3lkgrove/VoronZero/STLs/V0/Toolheads/Hotend_Mounts/Standard/[a]_Hotend_Mount_Revo_Voron.stl

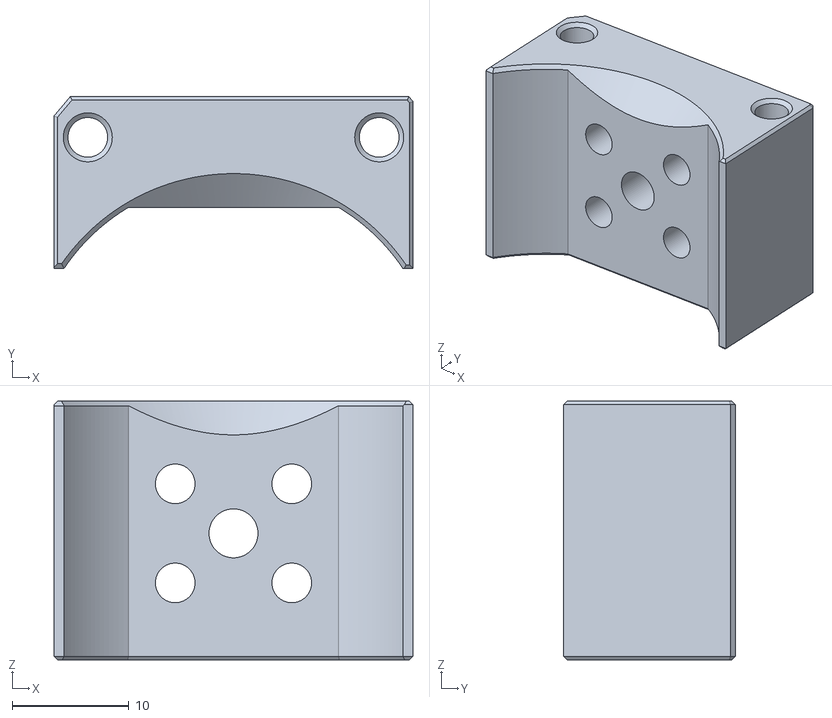
[picture p17: CAD file, 2025-04-02]
STLs/V0/Toolheads/Hotend_Mounts/Standard/[a]_Hotend_Mount_Revo_Voron.stl
30.8 x 14.7 x 22.2
