3lkgrove/VoronZero/STLs/V0/Toolheads/Mini_Stealthburner/[a]_MiniSB_Motor_Plate_x1.stl

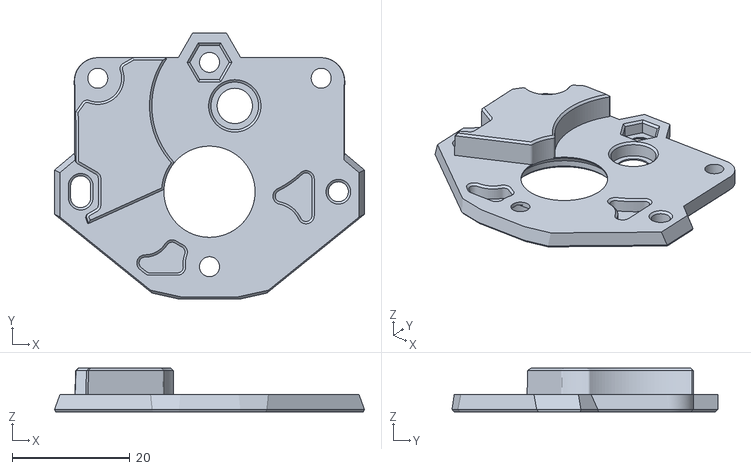
[picture p18: CAD file, 2025-04-02]
STLs/V0/Toolheads/Mini_Stealthburner/[a]_MiniSB_Motor_Plate_x1.stl
52.7 x 45.2 x 7.40
