3lkgrove/VoronZero/STLs/V0/Tools/V0_Extrusion_Drilling_Guide_x1.STL

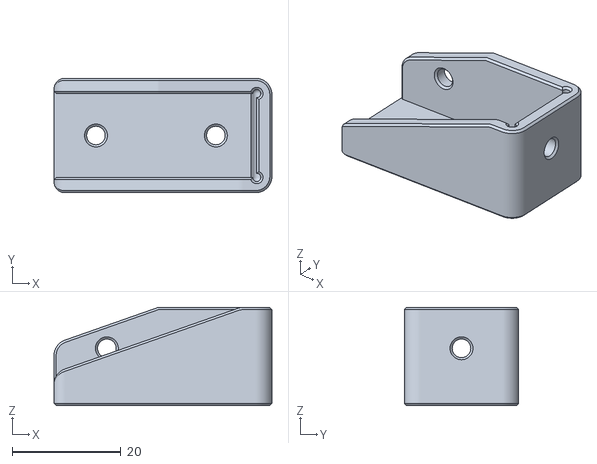
[picture p19: CAD file, 2025-04-02]
STLs/V0/Tools/V0_Extrusion_Drilling_Guide_x1.STL
40.0 x 21.0 x 18.0
