3lkgrove/VoronZero/STLs/V0/Tophat/TH_Lower_Clip_Mirror_x3.stl

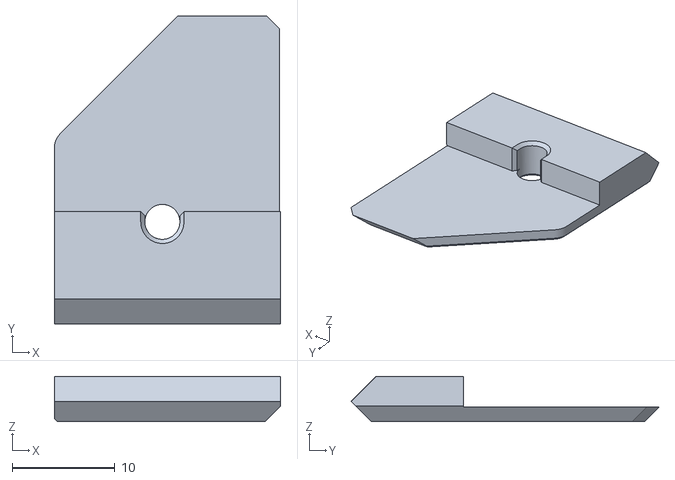
[picture p20: CAD file, 2025-04-02]
STLs/V0/Tophat/TH_Lower_Clip_Mirror_x3.stl
22.0 x 29.9 x 4.40
