3lkgrove/VoronZero/STLs/V0/XY_Joint_Left_Lower_x1.stl

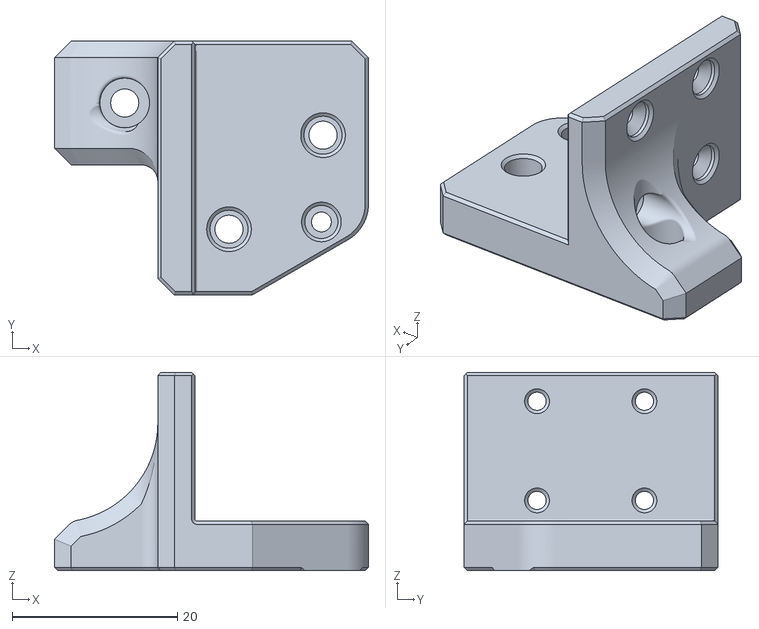
[picture p21: CAD file, 2025-04-02]
STLs/V0/XY_Joint_Left_Lower_x1.stl
38.0 x 30.7 x 24.0
