3lkgrove/VoronZero/STLs/Kirigami/VORON_v0.2_stealth_chain_mount_5mm_spacer.stl

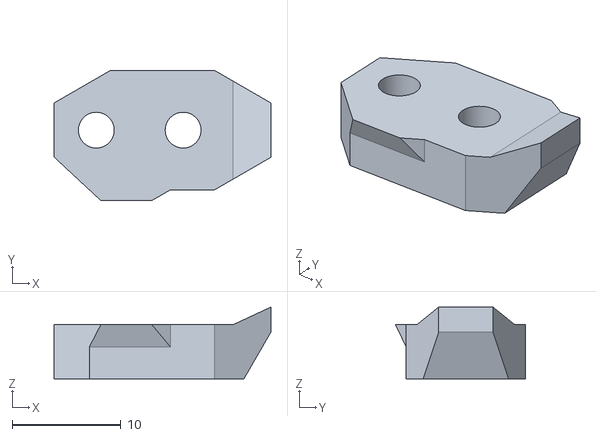
[picture p22: CAD file, 2025-04-02]
STLs/Kirigami/VORON_v0.2_stealth_chain_mount_5mm_spacer.stl
20.0 x 12.0 x 6.63
