3lkgrove/VoronZero/STLs/Umbilical/ToolheadSpacer_with_StrainRelief.STL

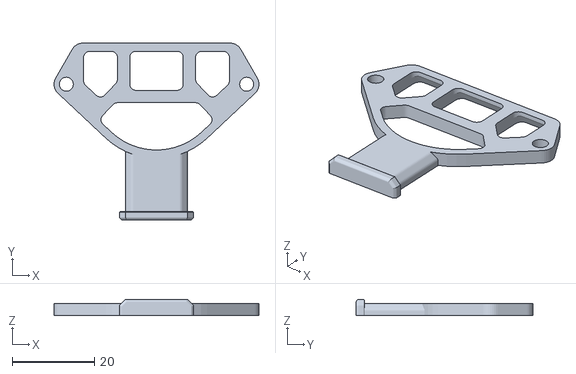
[picture p23: CAD file, 2025-04-06]
STLs/Umbilical/ToolheadSpacer_with_StrainRelief.STL
49.8 x 43.0 x 4.00
