3lkgrove/VoronZero/STLs/V0/Display/[a]_Display_Faceplate_x1.stl

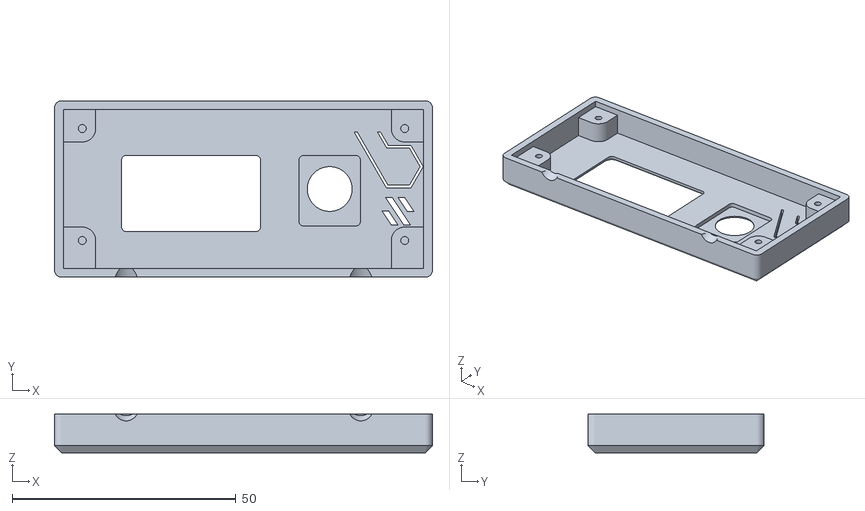
[picture p24: CAD file, 2025-04-02]
STLs/V0/Display/[a]_Display_Faceplate_x1.stl
84.4 x 39.4 x 8.63
