3lkgrove/VoronZero/STLs/V0/Electronics/RPi_or_BTT-Pico_Mount.STL

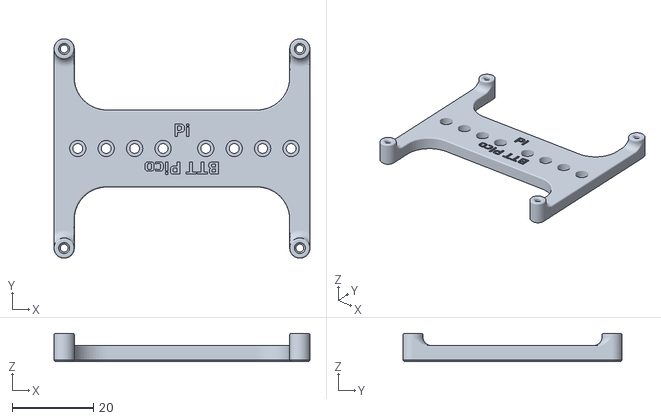
[picture p25: CAD file, 2025-04-02]
STLs/V0/Electronics/RPi_or_BTT-Pico_Mount.STL
63.0 x 54.0 x 7.00
