3lkgrove/VoronZero/STLs/V0/Multibody_STLs/Skirts/Front_Left_Skirt_Multibody_x1.stl

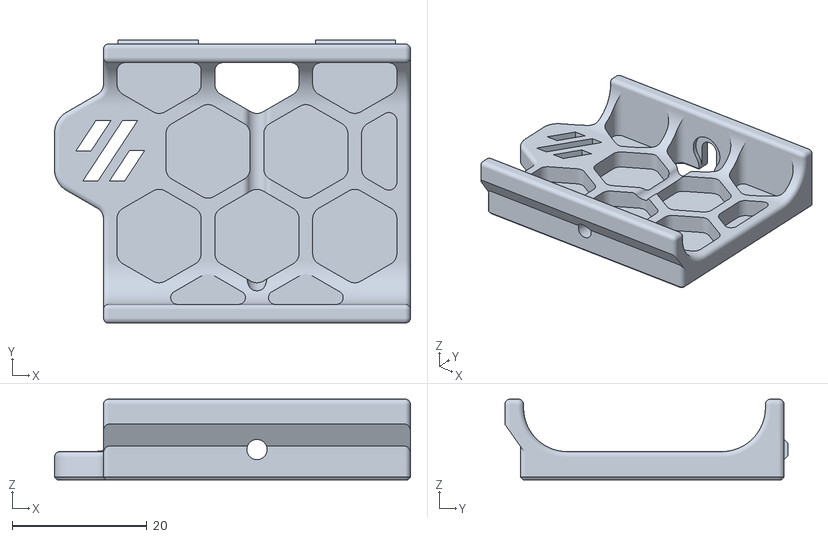
[picture p26: CAD file, 2025-04-02]
STLs/V0/Multibody_STLs/Skirts/Front_Left_Skirt_Multibody_x1.stl
52.9 x 42.1 x 12.0
