3lkgrove/VoronZero/STLs/V0/Skirts/Foot_Rear_Right_Plain.STL

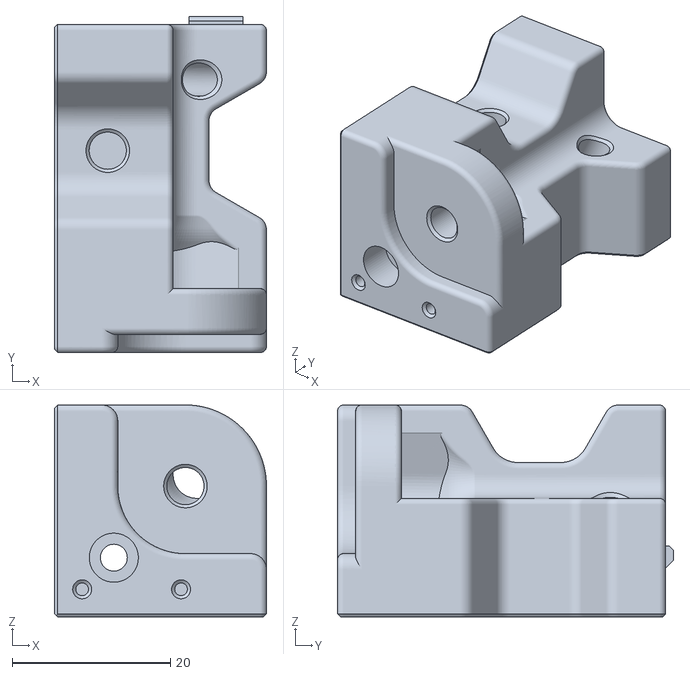
[picture p27: CAD file, 2025-04-02]
STLs/V0/Skirts/Foot_Rear_Right_Plain.STL
26.8 x 42.5 x 26.8
