3lkgrove/VoronZero/STLs/V0/Toolheads/ADXL_Mounts/MiniSB_adxl_mount_adafruit_19mm.stl

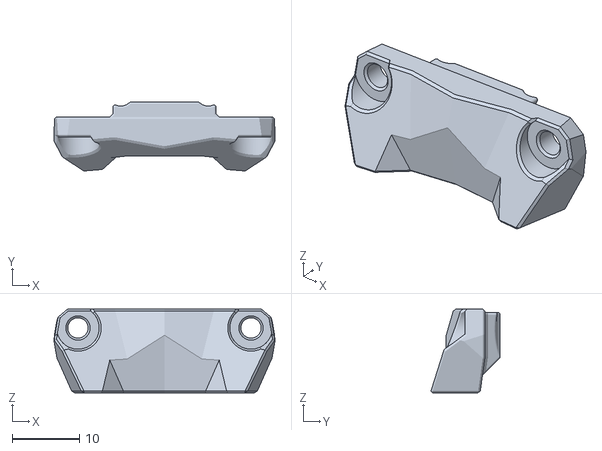
[picture p28: CAD file, 2025-04-02]
STLs/V0/Toolheads/ADXL_Mounts/MiniSB_adxl_mount_adafruit_19mm.stl
32.8 x 10.2 x 12.4
