3lkgrove/VoronZero/STLs/V0/Toolheads/Hotend_Mounts/Standard/[a]_Hotend_Mount_Formbot.stl

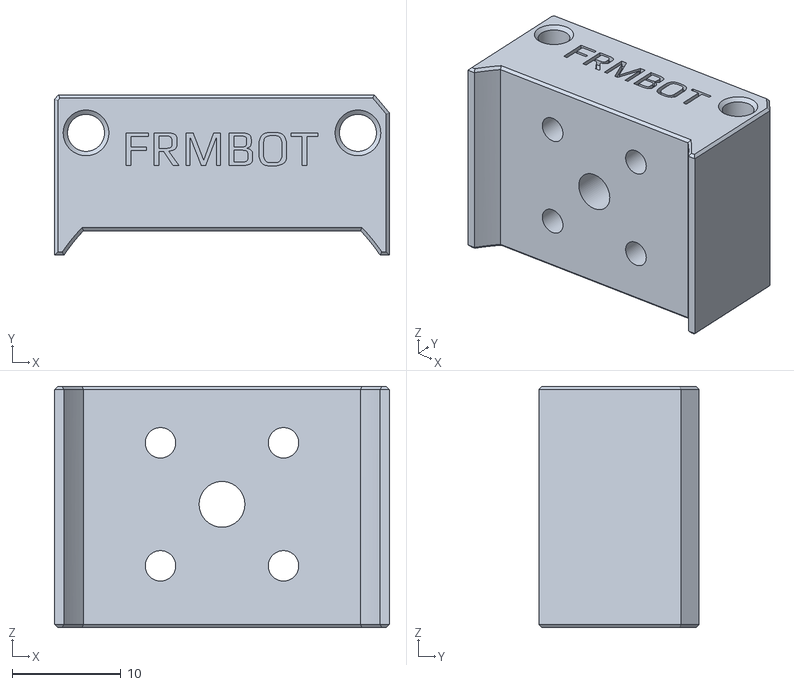
[picture p30: CAD file, 2025-04-02]
STLs/V0/Toolheads/Hotend_Mounts/Standard/[a]_Hotend_Mount_Formbot.stl
30.8 x 14.7 x 22.2
