3lkgrove/VoronZero/STLs/V0/Toolheads/Mini_Stealthburner/[a]_Guidler_x1.STL

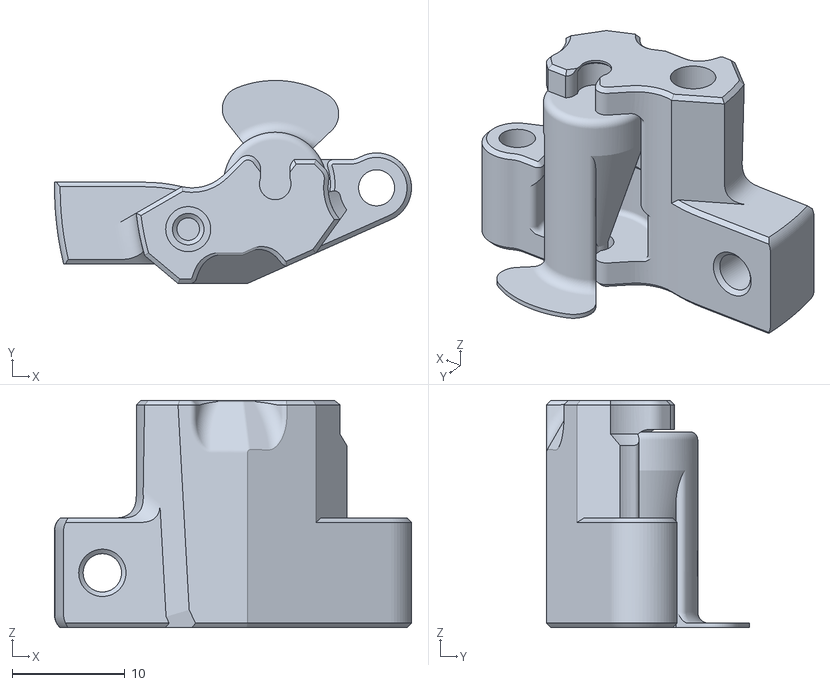
[picture p31: CAD file, 2025-04-02]
STLs/V0/Toolheads/Mini_Stealthburner/[a]_Guidler_x1.STL
31.7 x 18.0 x 20.2
