3lkgrove/VoronZero/STLs/V0/Tophat/TH_Hinge_A_Top_x1.stl

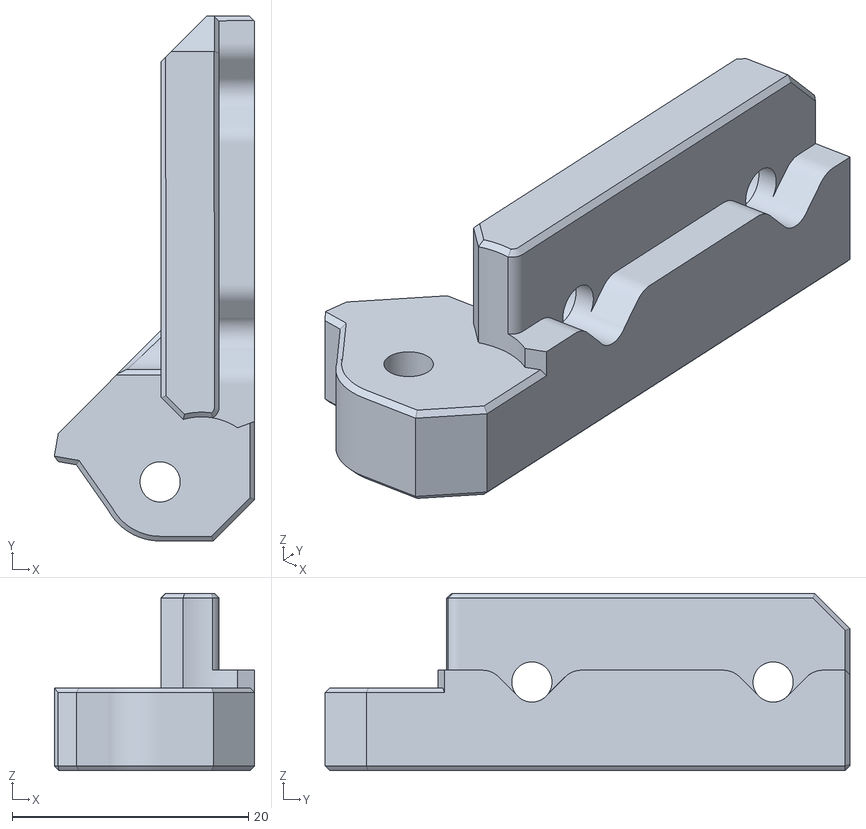
[picture p32: CAD file, 2025-04-02]
STLs/V0/Tophat/TH_Hinge_A_Top_x1.stl
17.0 x 44.4 x 15.0
