3lkgrove/VoronZero/STLs/Umbilical/FramePCBCover.STL

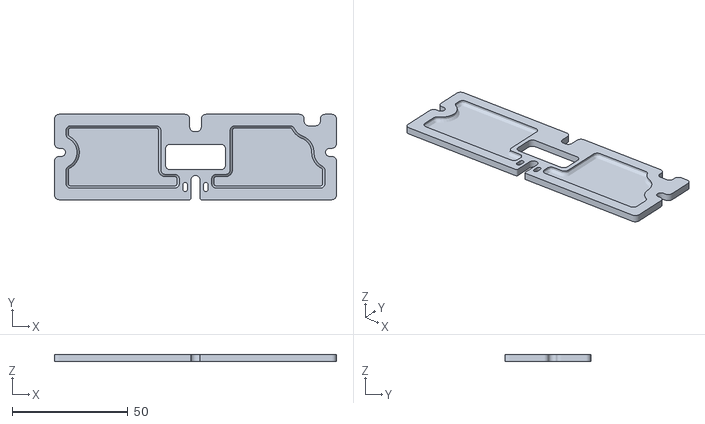
[picture p33: CAD file, 2025-04-06]
STLs/Umbilical/FramePCBCover.STL
122.0 x 37.0 x 3.00
