3lkgrove/VoronZero/STLs/V0/Display/Display_Knob_x1.stl

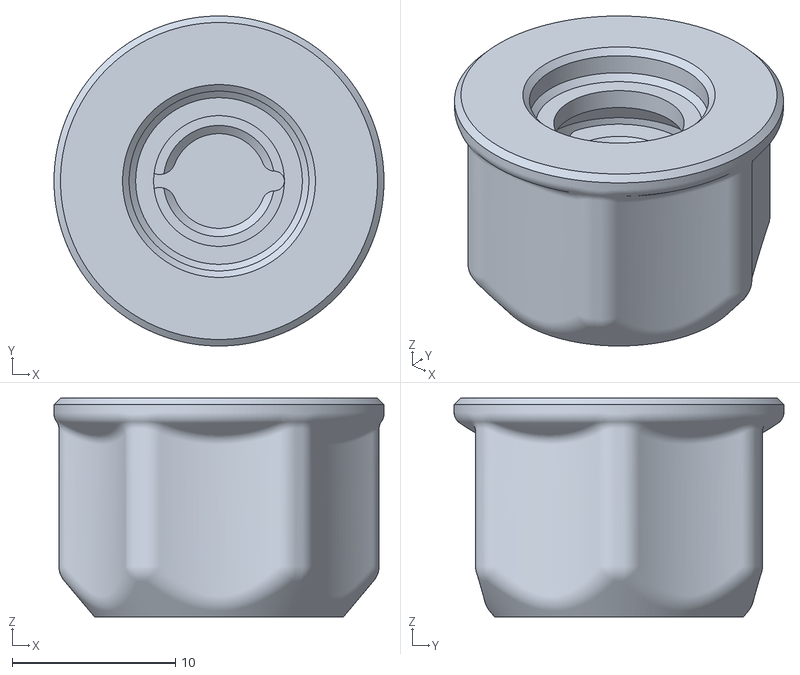
[picture p34: CAD file, 2025-04-02]
STLs/V0/Display/Display_Knob_x1.stl
20.2 x 20.2 x 13.4
