3lkgrove/VoronZero/STLs/V0/Electronics/Fan_Mount_Bottom_x1.stl

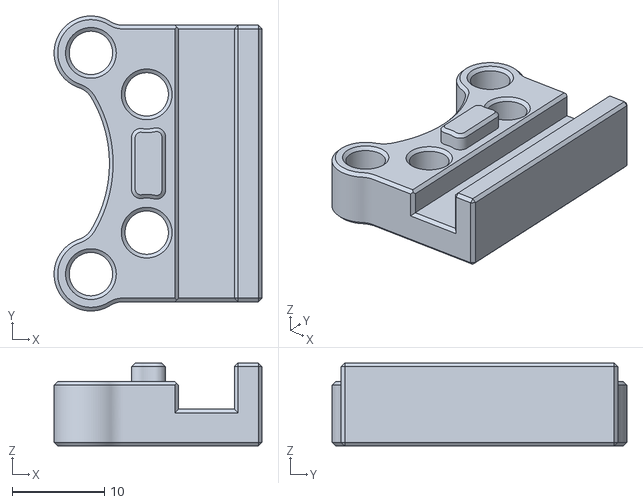
[picture p35: CAD file, 2025-04-02]
STLs/V0/Electronics/Fan_Mount_Bottom_x1.stl
22.5 x 32.0 x 9.00
