3lkgrove/VoronZero/STLs/V0/Front_Bed_Mount_x1.stl

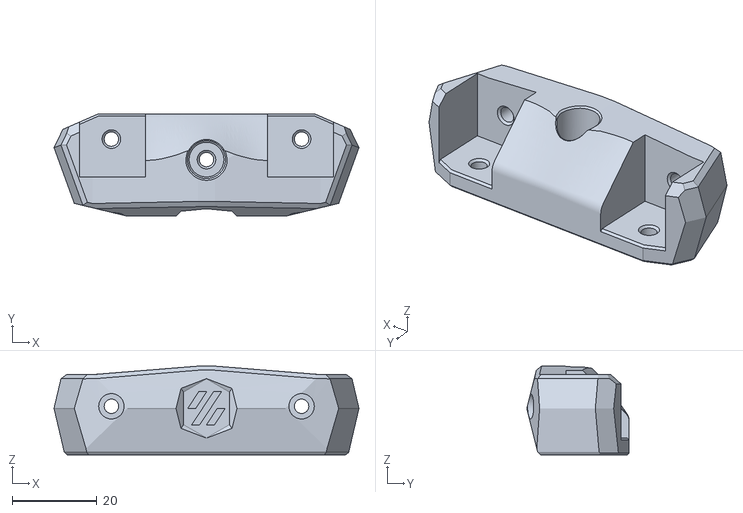
[picture p36: CAD file, 2025-04-02]
STLs/V0/Front_Bed_Mount_x1.stl
72.2 x 24.2 x 21.0
