3lkgrove/VoronZero/STLs/V0/Multibody_STLs/Skirts/Rear_Skirt_Multibody_x1.stl

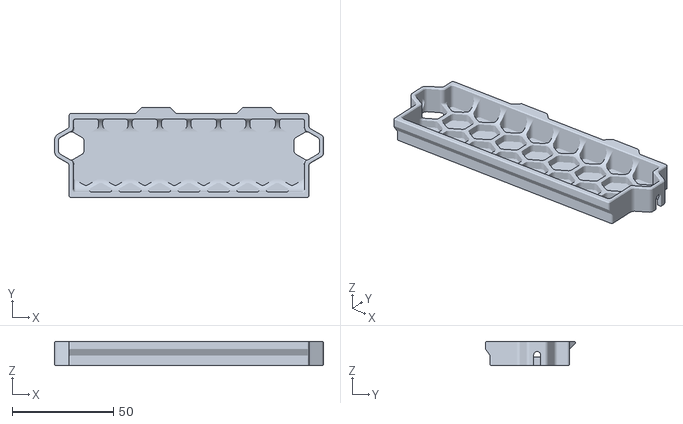
[picture p37: CAD file, 2025-04-02]
STLs/V0/Multibody_STLs/Skirts/Rear_Skirt_Multibody_x1.stl
132.8 x 44.5 x 12.0
