3lkgrove/VoronZero/STLs/V0/Panel_Mounting/Door_Handle_x1.STL

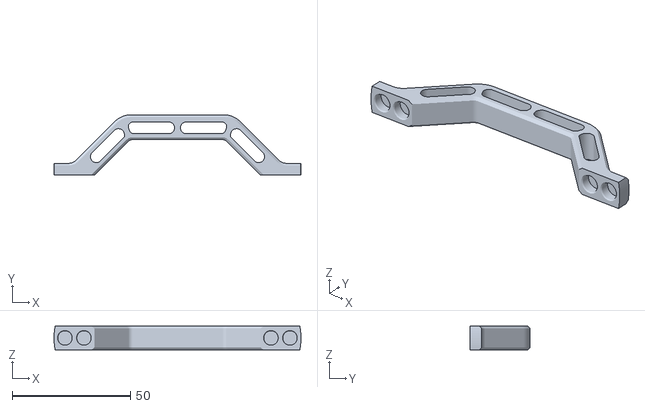
[picture p38: CAD file, 2025-04-02]
STLs/V0/Panel_Mounting/Door_Handle_x1.STL
104.3 x 25.5 x 10.0
