3lkgrove/VoronZero/STLs/V0/Skirts/Side_Skirt_x2.STL

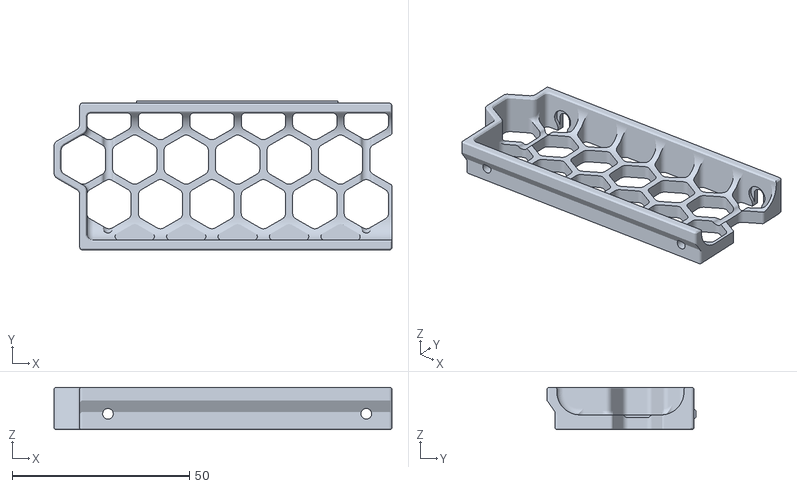
[picture p39: CAD file, 2025-04-02]
STLs/V0/Skirts/Side_Skirt_x2.STL
95.5 x 42.1 x 12.0
