3lkgrove/VoronZero/STLs/V0/Toolheads/Bowden/MiniSB_Bowden_Logo_Insert.stl

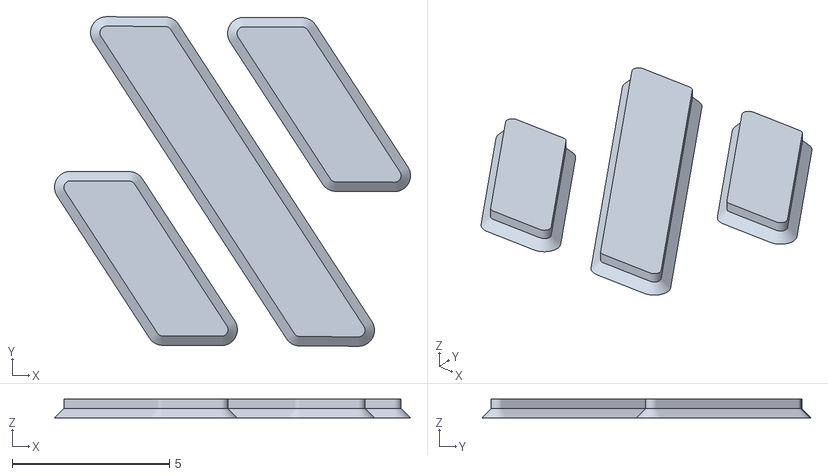
[picture p40: CAD file, 2025-04-02]
STLs/V0/Toolheads/Bowden/MiniSB_Bowden_Logo_Insert.stl
11.3 x 10.5 x 0.6
