3lkgrove/VoronZero/STLs/V0/Toolheads/Mini_Stealthburner/[a]_Shuttle_x1.stl

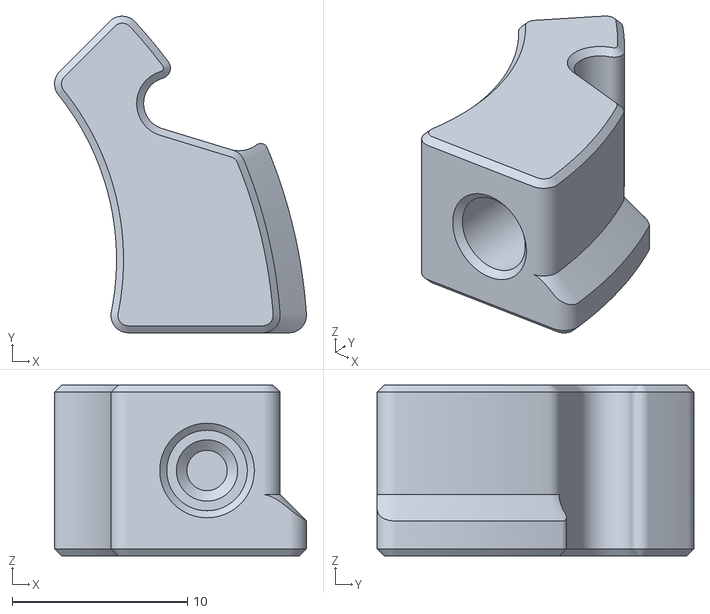
[picture p42: CAD file, 2025-04-02]
STLs/V0/Toolheads/Mini_Stealthburner/[a]_Shuttle_x1.stl
14.4 x 18.1 x 9.75
