3lkgrove/VoronZero/STLs/V0/Tools/MGN7_Rail_Guide_x2.STL

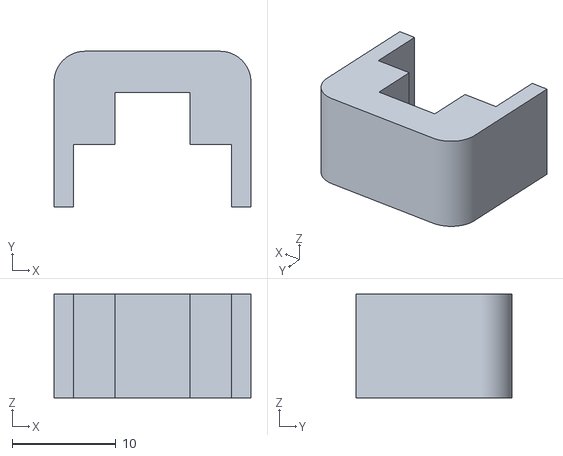
[picture p43: CAD file, 2025-04-02]
STLs/V0/Tools/MGN7_Rail_Guide_x2.STL
19.0 x 15.0 x 10.0
