3lkgrove/VoronZero/STLs/Kirigami/VORON_v0.2_stealth_chain_mount.stl

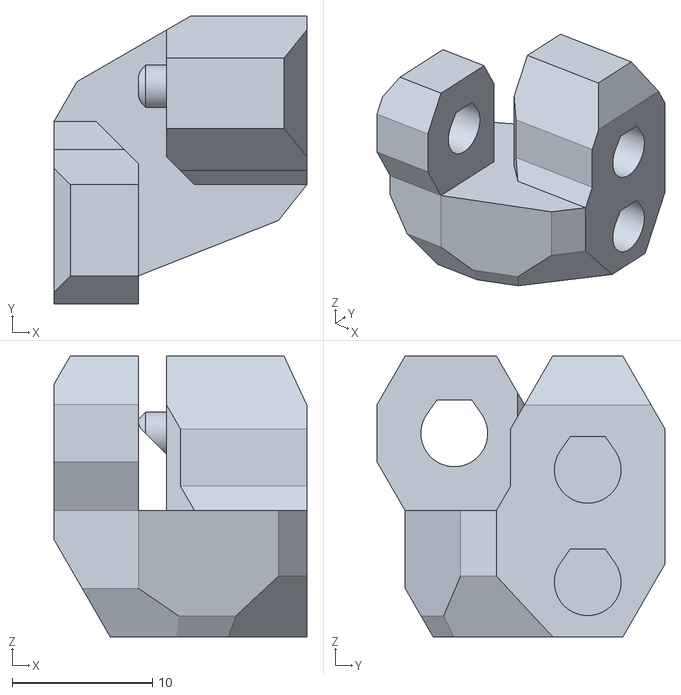
[picture p44: CAD file, 2025-04-02]
STLs/Kirigami/VORON_v0.2_stealth_chain_mount.stl
18.0 x 20.5 x 20.0
