3lkgrove/VoronZero/STLs/Umbilical/Multicolor PCB Cover/PCB_Text.stl

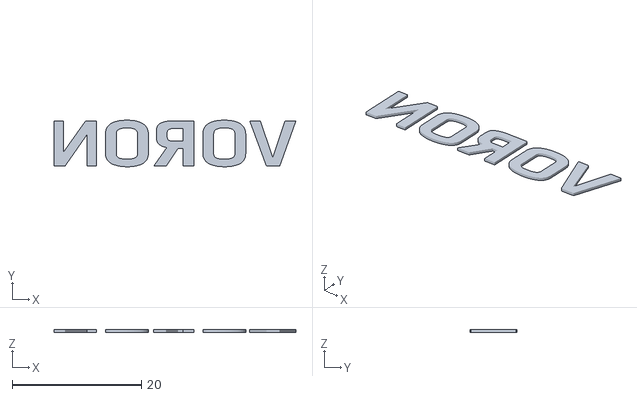
[picture p45: CAD file, 2025-04-06]
STLs/Umbilical/Multicolor PCB Cover/PCB_Text.stl
37.4 x 7.22 x 0.4
