3lkgrove/VoronZero/STLs/Umbilical/PTFE_Guide.stl

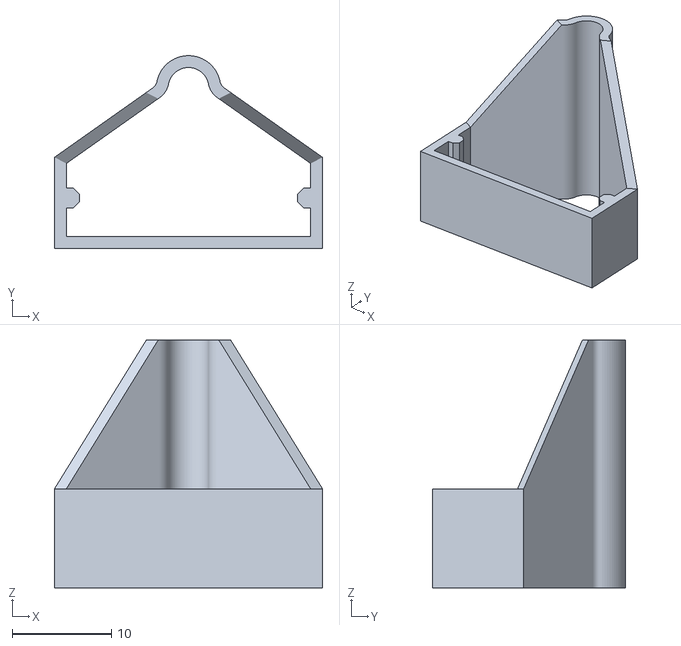
[picture p46: CAD file, 2025-04-06]
STLs/Umbilical/PTFE_Guide.stl
27.0 x 19.5 x 25.0
