3lkgrove/VoronZero/STLs/V0/B_Drive_Frame_Lower_x1.stl

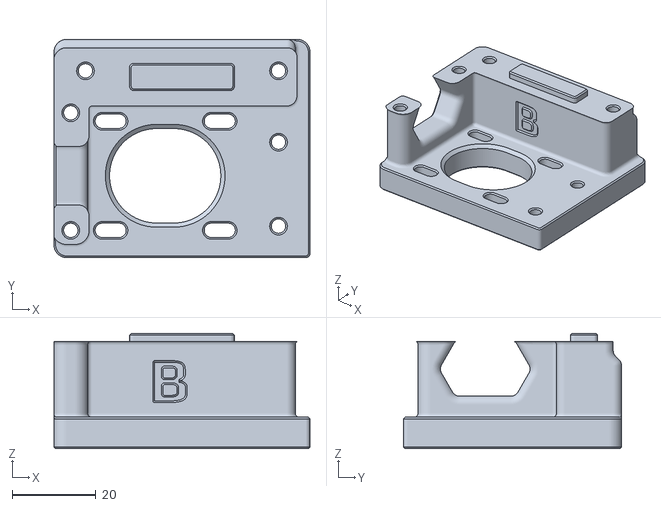
[picture p47: CAD file, 2025-04-02]
STLs/V0/B_Drive_Frame_Lower_x1.stl
61.0 x 52.0 x 27.5
