3lkgrove/VoronZero/STLs/V0/Electronics/Fly_Gemini_V2_Din_Mount_2pc.stl

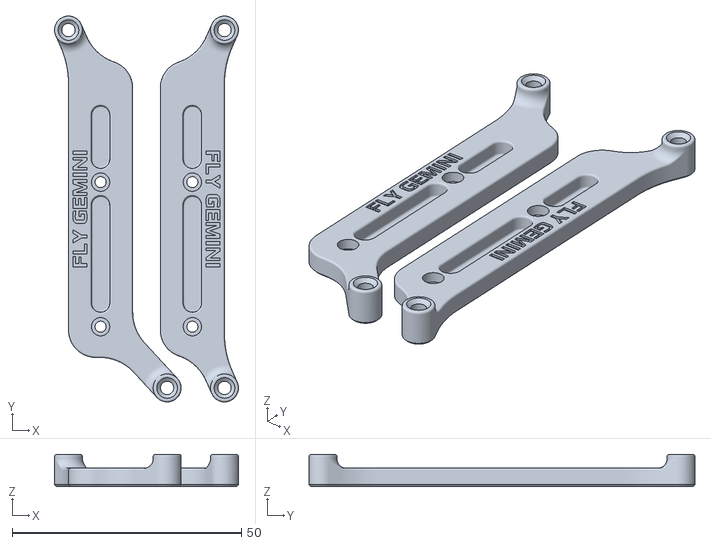
[picture p48: CAD file, 2025-04-02]
STLs/V0/Electronics/Fly_Gemini_V2_Din_Mount_2pc.stl
40.1 x 84.1 x 7.00
