3lkgrove/VoronZero/STLs/V0/Multibody_STLs/Skirts/Headless_Skirt_Insert_Multibody_x1.stl

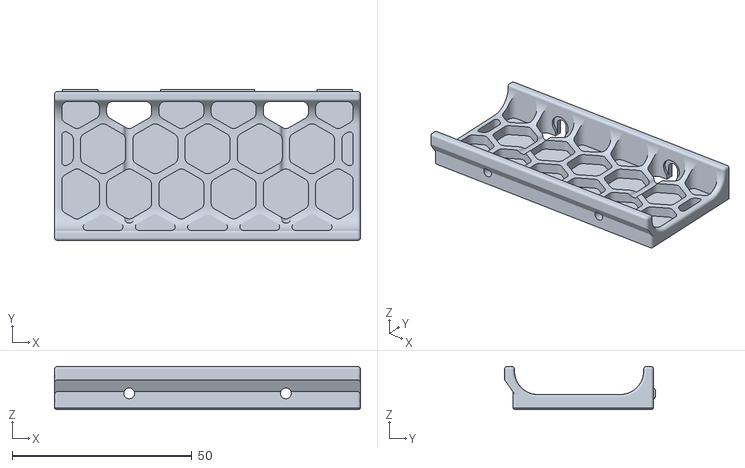
[picture p49: CAD file, 2025-04-02]
STLs/V0/Multibody_STLs/Skirts/Headless_Skirt_Insert_Multibody_x1.stl
85.2 x 42.0 x 12.0
