3lkgrove/VoronZero/STLs/V0/Panel_Mounting/Front_Top_Right_Hinge_x1.stl

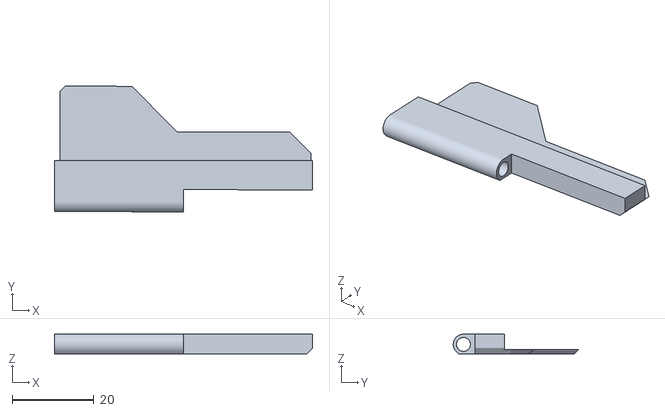
[picture p50: CAD file, 2025-04-02]
STLs/V0/Panel_Mounting/Front_Top_Right_Hinge_x1.stl
63.0 x 30.7 x 4.80
