3lkgrove/VoronZero/STLs/V0/Skirts/Foot_Rear_Right_FRS_x1.STL

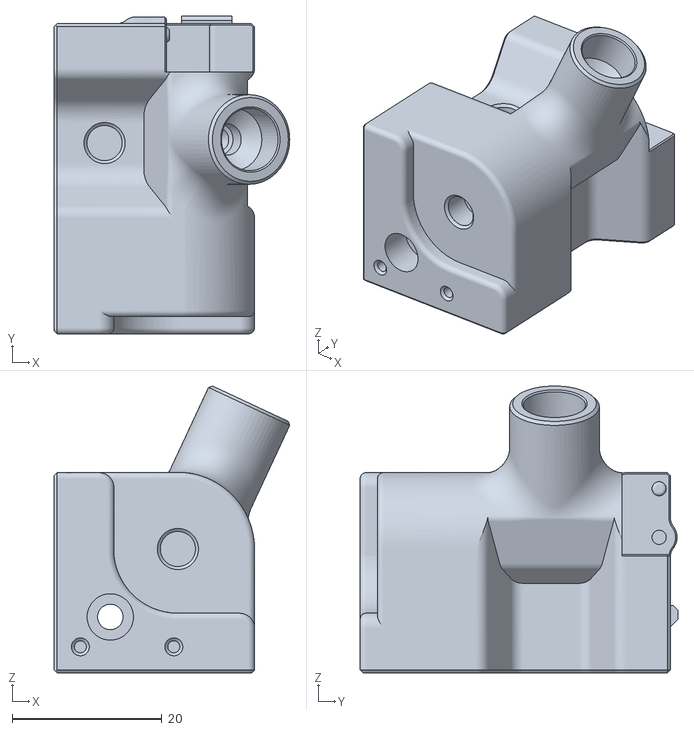
[picture p51: CAD file, 2025-04-02]
STLs/V0/Skirts/Foot_Rear_Right_FRS_x1.STL
31.5 x 42.5 x 38.4
