3lkgrove/VoronZero/STLs/V0/Toolheads/Hotend_Mounts/Fan_Saver/[a]_FS_Hotend_Mount_Dragonfly_BMS_7_FINS.stl

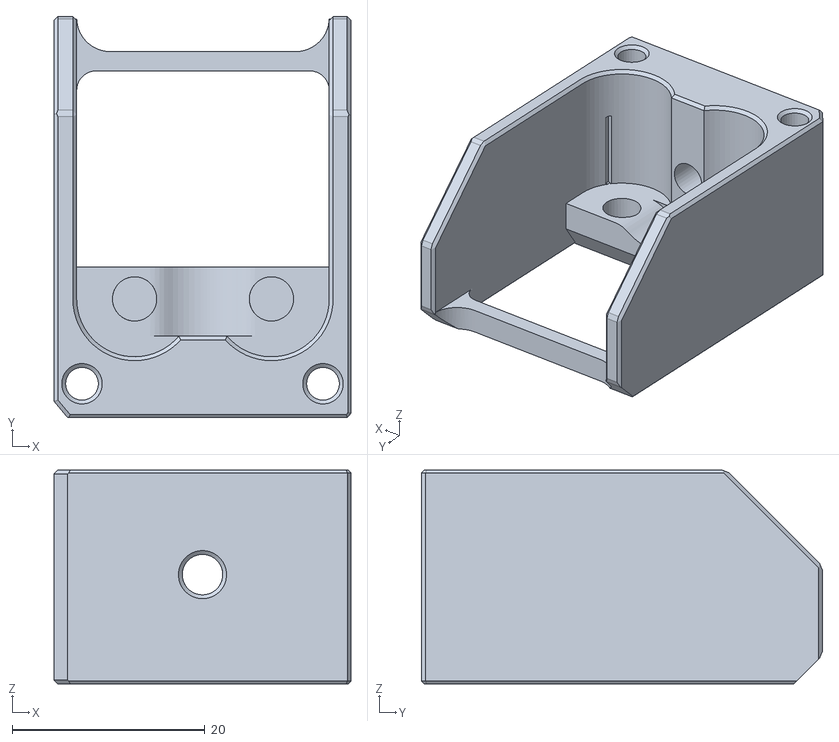
[picture p52: CAD file, 2025-04-02]
STLs/V0/Toolheads/Hotend_Mounts/Fan_Saver/[a]_FS_Hotend_Mount_Dragonfly_BMS_7_FINS.stl
30.8 x 41.6 x 22.2
