3lkgrove/VoronZero/STLs/V0/Toolheads/Hotend_Mounts/Standard/[a]_Hotend_Mount_Drop_Effect_XG.stl

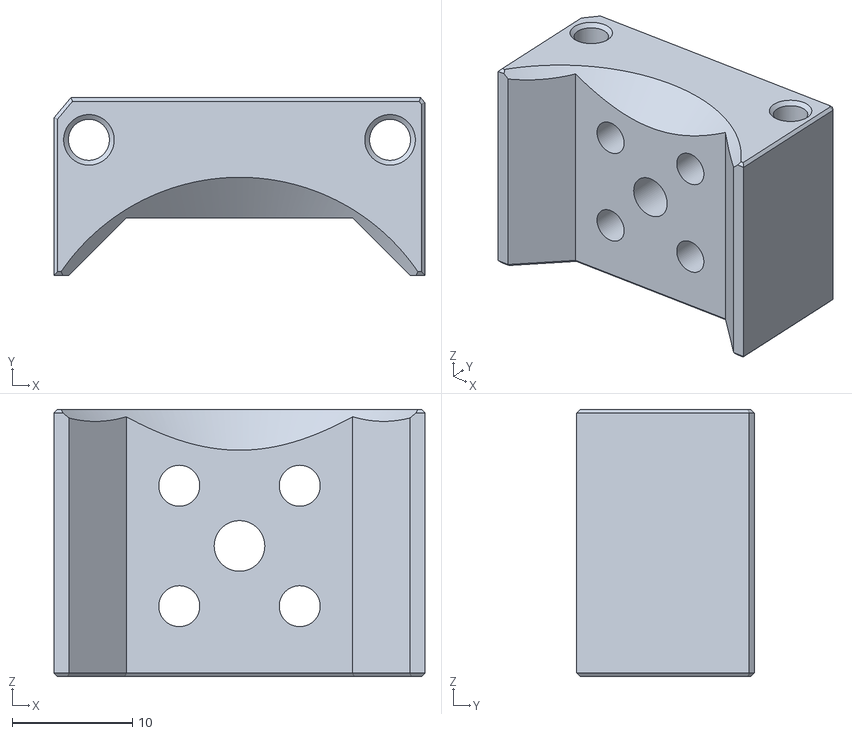
[picture p53: CAD file, 2025-04-02]
STLs/V0/Toolheads/Hotend_Mounts/Standard/[a]_Hotend_Mount_Drop_Effect_XG.stl
30.8 x 14.7 x 22.2
