3lkgrove/VoronZero/STLs/V0/Toolheads/Mini_Stealthburner/Strain_Relief_Spacer_x2.stl

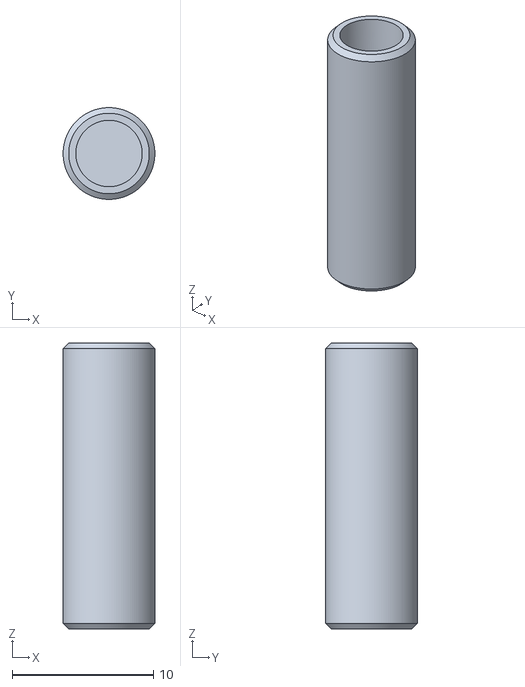
[picture p54: CAD file, 2025-04-02]
STLs/V0/Toolheads/Mini_Stealthburner/Strain_Relief_Spacer_x2.stl
6.50 x 6.50 x 20.2
