3lkgrove/VoronZero/STLs/V0/Tools/BMG_Shaft_Mod_Spacer_x1.STL

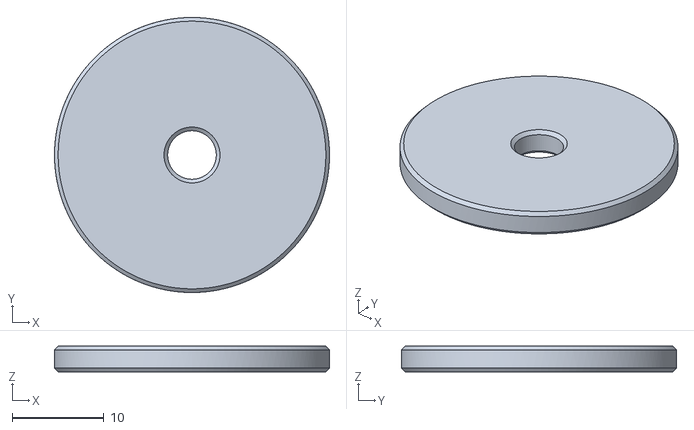
[picture p55: CAD file, 2025-04-02]
STLs/V0/Tools/BMG_Shaft_Mod_Spacer_x1.STL
30.0 x 30.0 x 2.80
