3lkgrove/VoronZero/STLs/V0/Tophat/TH_Side_Clip_x4.stl

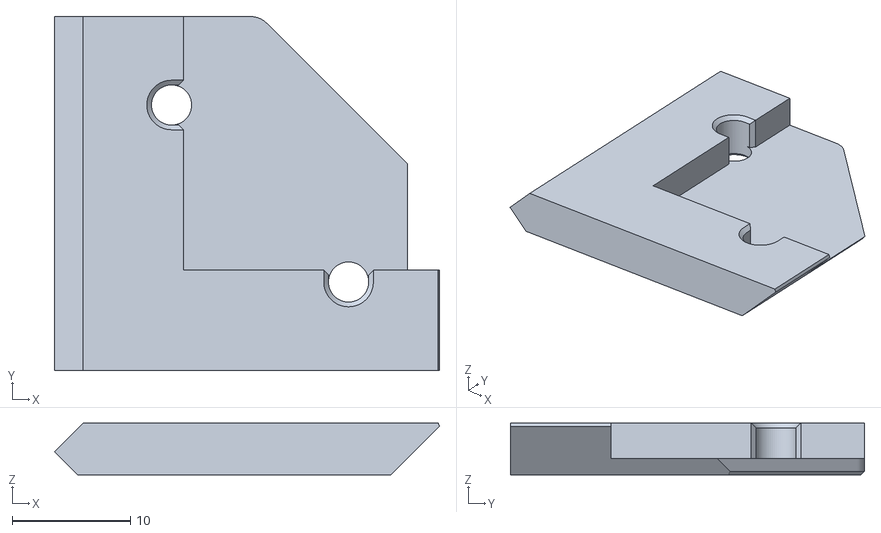
[picture p56: CAD file, 2025-04-02]
STLs/V0/Tophat/TH_Side_Clip_x4.stl
32.6 x 30.0 x 4.40
