3lkgrove/VoronZero/STLs/V0/Display/[c]_Display_Diffuser_x1.STL

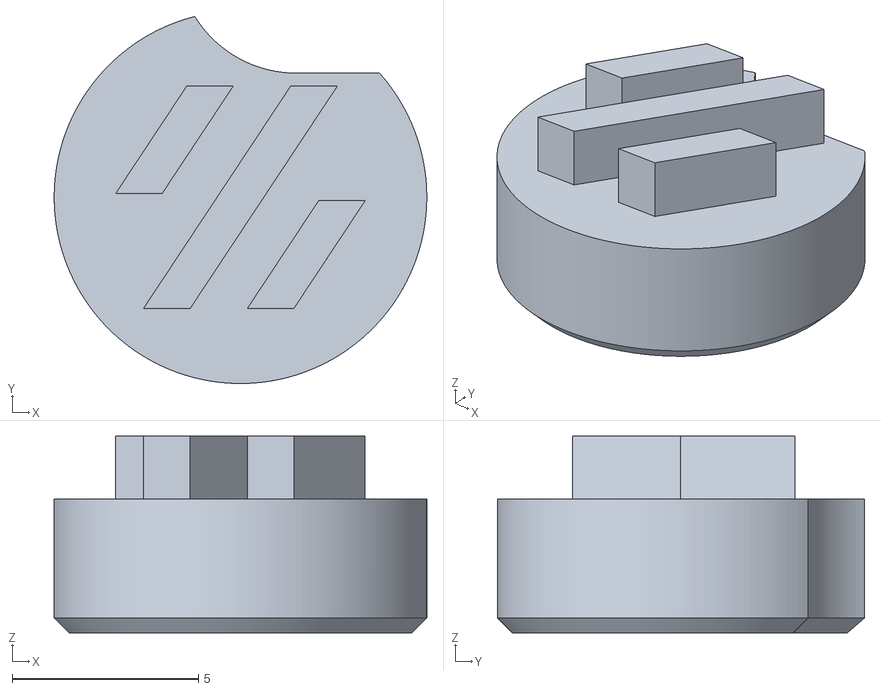
[picture p57: CAD file, 2025-04-02]
STLs/V0/Display/[c]_Display_Diffuser_x1.STL
10.00 x 9.85 x 5.28
