3lkgrove/VoronZero/STLs/V0/Electronics/SKR_3_Din_Mount.stl

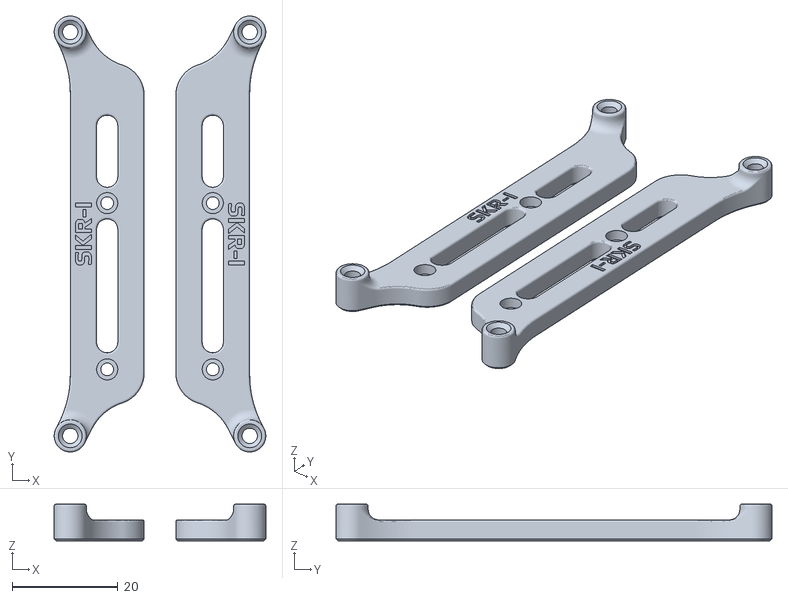
[picture p58: CAD file, 2025-04-02]
STLs/V0/Electronics/SKR_3_Din_Mount.stl
40.1 x 82.6 x 7.00
