3lkgrove/VoronZero/STLs/V0/Panel_Mounting/Right_Bottom_Front_Hinge_x1.stl

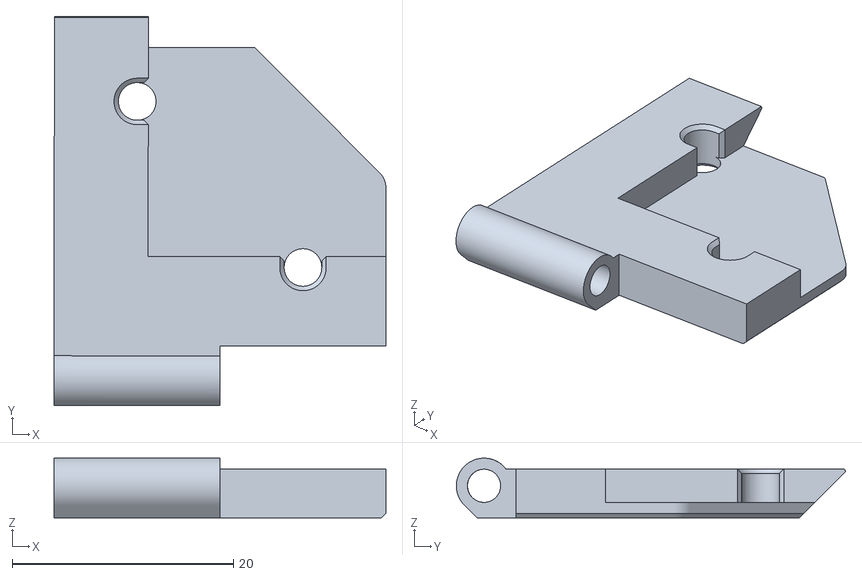
[picture p59: CAD file, 2025-04-02]
STLs/V0/Panel_Mounting/Right_Bottom_Front_Hinge_x1.stl
30.0 x 35.2 x 5.40
