3lkgrove/VoronZero/STLs/V0/Skirts/Foot_Rear_Left_Inlet_x1.STL

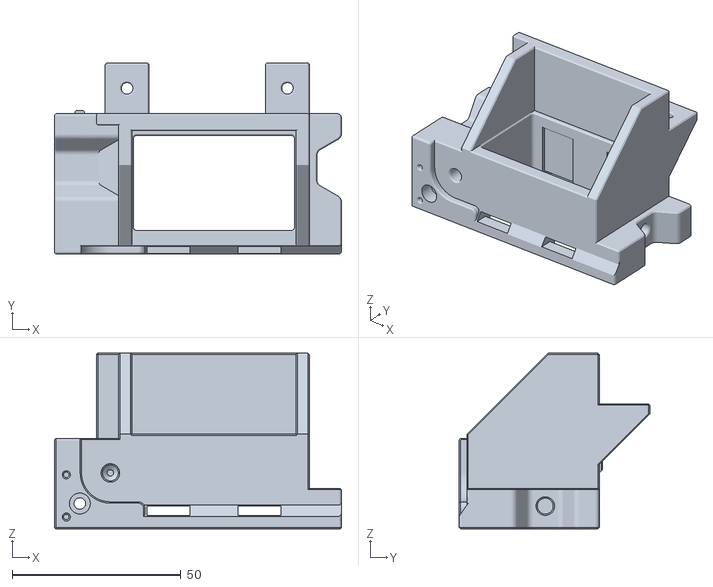
[picture p60: CAD file, 2025-04-02]
STLs/V0/Skirts/Foot_Rear_Left_Inlet_x1.STL
84.9 x 56.5 x 52.0
