3lkgrove/VoronZero/STLs/V0/Spool_Holder_x1.STL

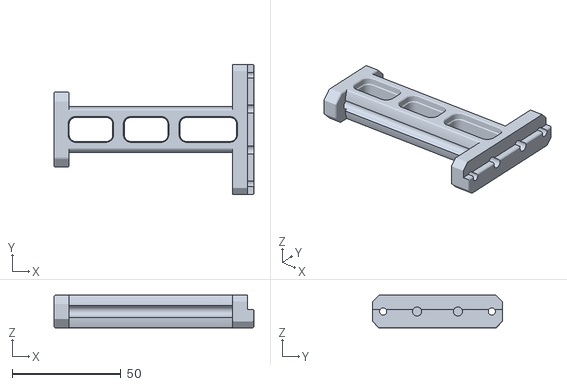
[picture p61: CAD file, 2025-04-02]
STLs/V0/Spool_Holder_x1.STL
92.0 x 60.0 x 15.0
