3lkgrove/VoronZero/STLs/V0/Toolheads/Hotend_Mounts/Fan_Saver/[a]_FS_Hotend_Mount_Formbot.stl

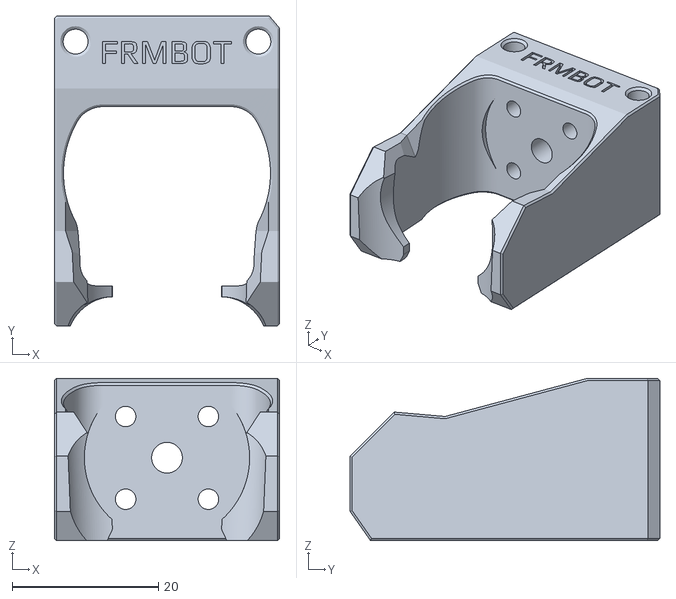
[picture p62: CAD file, 2025-04-02]
STLs/V0/Toolheads/Hotend_Mounts/Fan_Saver/[a]_FS_Hotend_Mount_Formbot.stl
30.8 x 42.4 x 22.2
