3lkgrove/VoronZero/STLs/V0/Toolheads/Mini_Stealthburner/[a]_Latch_x1.stl

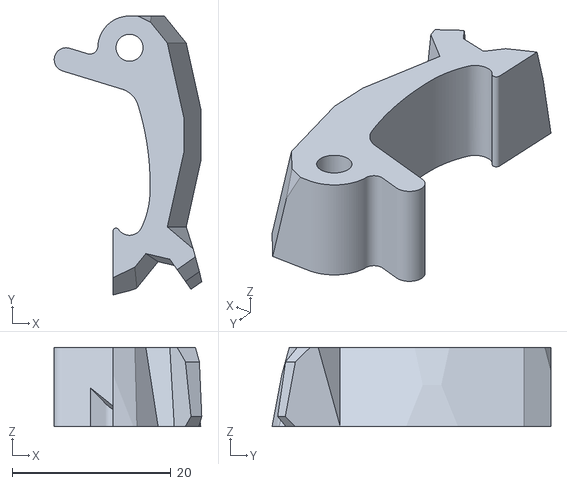
[picture p63: CAD file, 2025-04-02]
STLs/V0/Toolheads/Mini_Stealthburner/[a]_Latch_x1.stl
18.6 x 35.2 x 10.0
