3lkgrove/VoronZero/STLs/V0/Tools/Swiss_Army_Jig_x1.STL

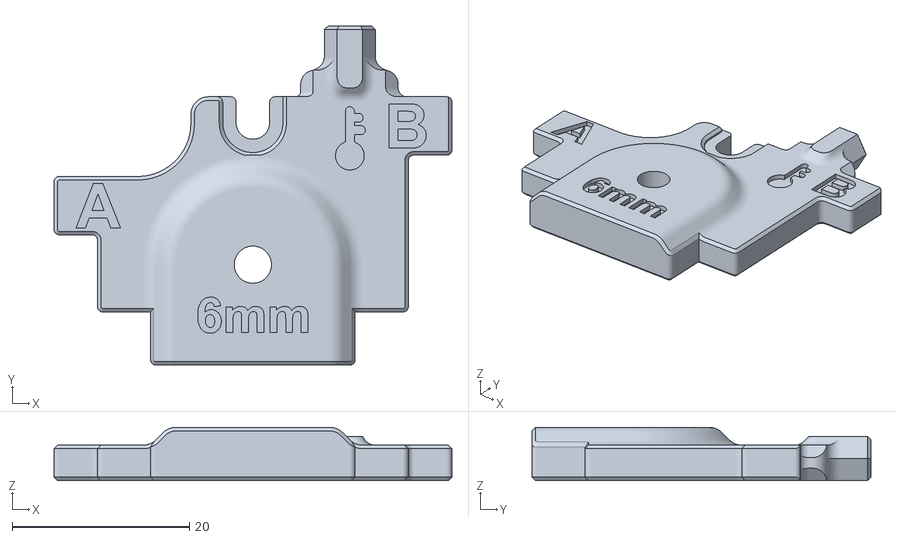
[picture p64: CAD file, 2025-04-02]
STLs/V0/Tools/Swiss_Army_Jig_x1.STL
44.9 x 38.3 x 6.00
