3lkgrove/VoronZero/STLs/V0/Tophat/TH_Hinge_B_Bottom_x1.stl

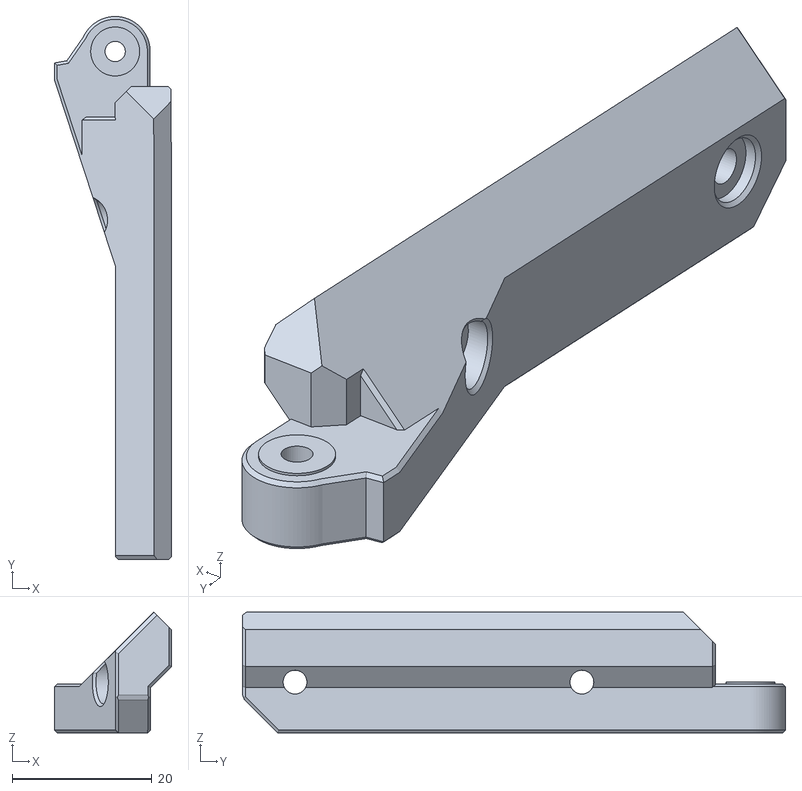
[picture p65: CAD file, 2025-04-02]
STLs/V0/Tophat/TH_Hinge_B_Bottom_x1.stl
16.8 x 77.6 x 17.2
