3lkgrove/VoronZero/STLs/V0/B_Drive_Frame_Upper_x1.stl

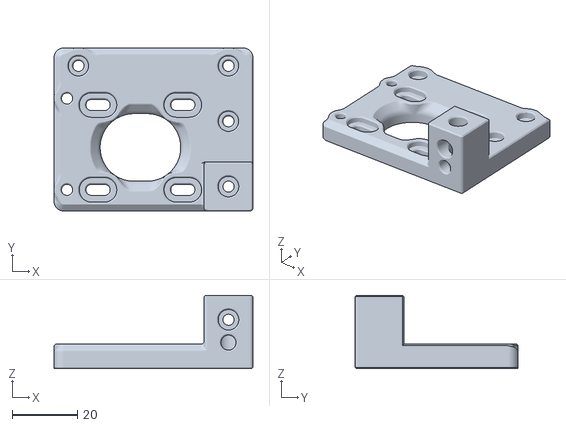
[picture p66: CAD file, 2025-04-02]
STLs/V0/B_Drive_Frame_Upper_x1.stl
61.0 x 50.0 x 22.5
