3lkgrove/VoronZero/STLs/V0/Electronics/SKR_E3_V3_Din_Mount.STL

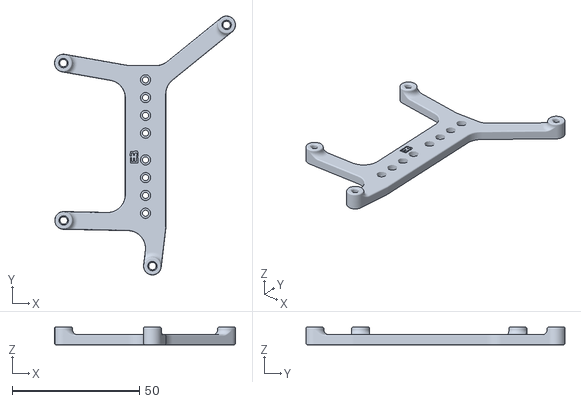
[picture p67: CAD file, 2025-04-02]
STLs/V0/Electronics/SKR_E3_V3_Din_Mount.STL
71.2 x 101.9 x 7.00
