3lkgrove/VoronZero/STLs/V0/Multibody_STLs/Skirts/Side_Skirt_Multibody_x2.stl

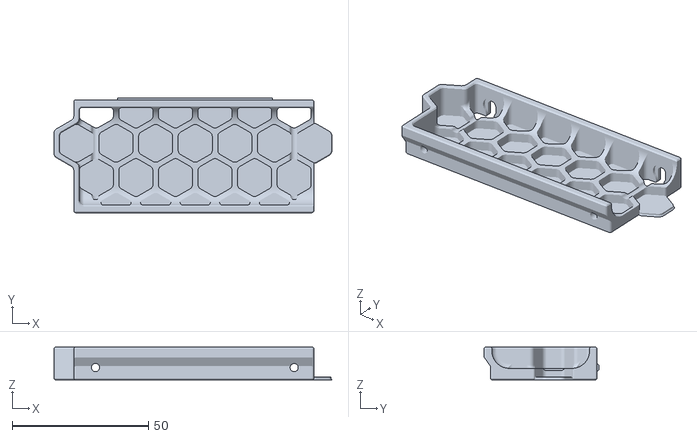
[picture p68: CAD file, 2025-04-02]
STLs/V0/Multibody_STLs/Skirts/Side_Skirt_Multibody_x2.stl
102.1 x 42.1 x 12.0
