3lkgrove/VoronZero/STLs/V0/Panel_Mounting/Front_Bottom_Left_Clip_x1.stl

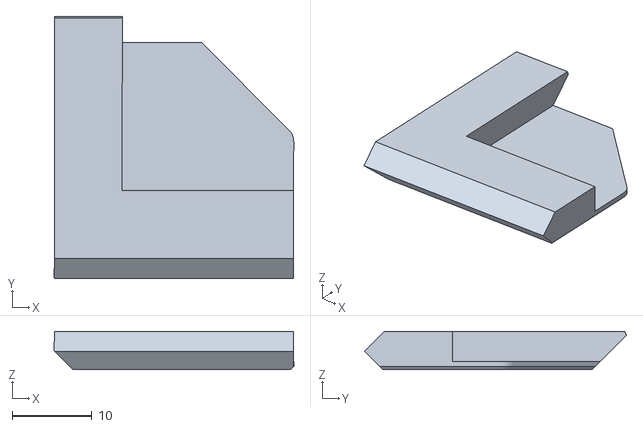
[picture p69: CAD file, 2025-04-02]
STLs/V0/Panel_Mounting/Front_Bottom_Left_Clip_x1.stl
30.0 x 32.8 x 4.80
