3lkgrove/VoronZero/STLs/V0/Skirts/Front_Skirt_A_x1.STL

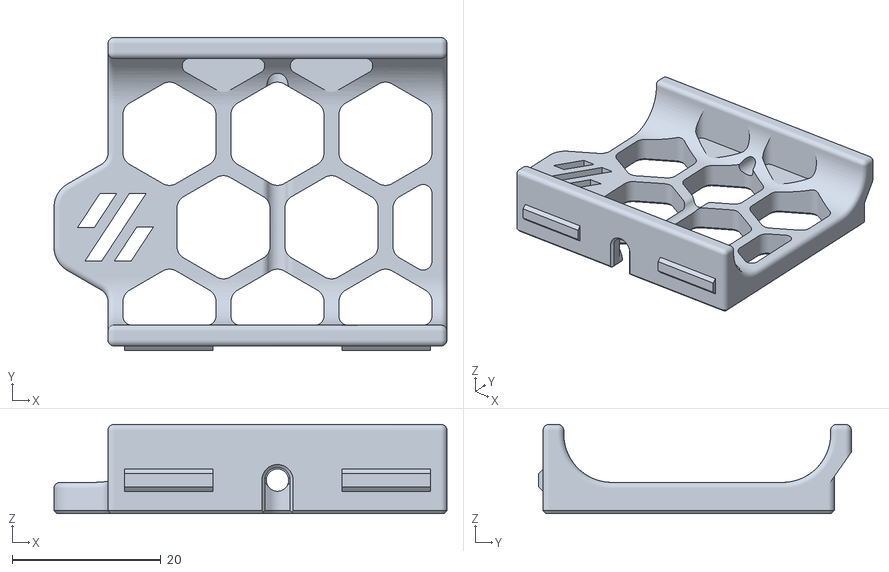
[picture p70: CAD file, 2025-04-02]
STLs/V0/Skirts/Front_Skirt_A_x1.STL
52.9 x 42.1 x 12.0
