3lkgrove/VoronZero/STLs/V0/Toolheads/Hotend_Mounts/Standard/[a]_Hotend_Mount_MicroSwiss_All_Metal.stl

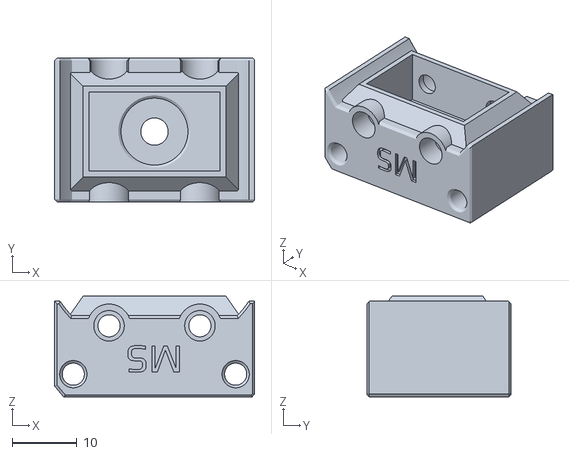
[picture p71: CAD file, 2025-04-02]
STLs/V0/Toolheads/Hotend_Mounts/Standard/[a]_Hotend_Mount_MicroSwiss_All_Metal.stl
30.8 x 22.2 x 15.5
