3lkgrove/VoronZero/STLs/V0/Toolheads/Mini_Stealthburner/[a]_MiniSB_MidBody_x1.STL

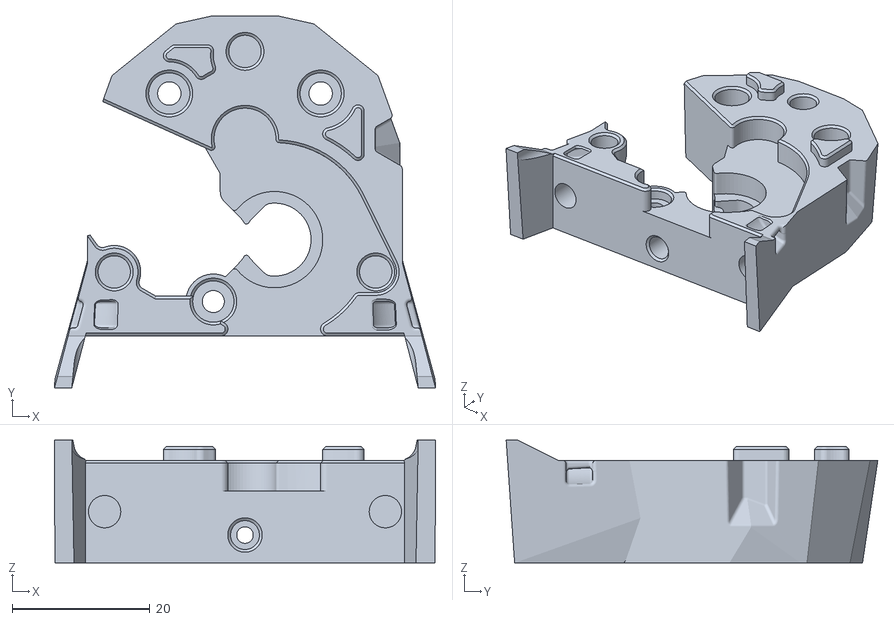
[picture p72: CAD file, 2025-04-02]
STLs/V0/Toolheads/Mini_Stealthburner/[a]_MiniSB_MidBody_x1.STL
55.4 x 54.0 x 17.8
