3lkgrove/VoronZero/STLs/Kirigami/kirigami_wago_mount.stl

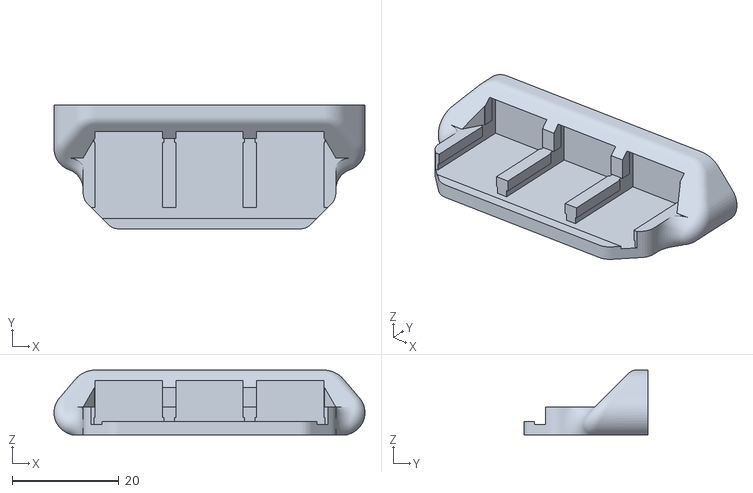
[picture p73: CAD file, 2025-04-02]
STLs/Kirigami/kirigami_wago_mount.stl
58.4 x 23.2 x 12.2
