3lkgrove/VoronZero/STLs/V0/[a]_9mm_Spacer_x6.stl

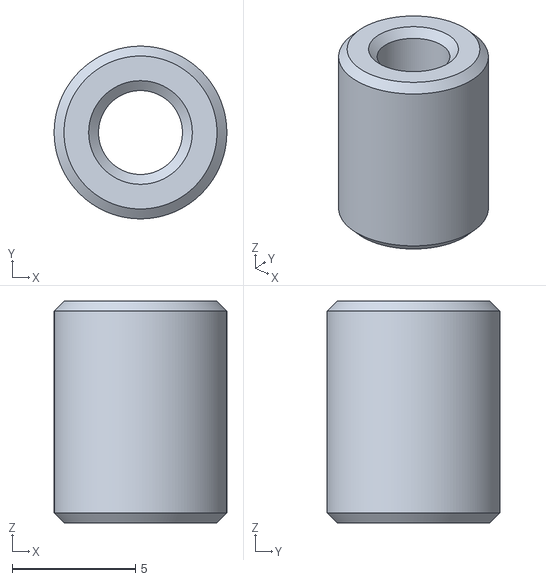
[picture p74: CAD file, 2025-04-02]
STLs/V0/[a]_9mm_Spacer_x6.stl
7.00 x 7.00 x 9.00
