3lkgrove/VoronZero/STLs/V0/Electronics/Fan_Mount_Top_x1.stl

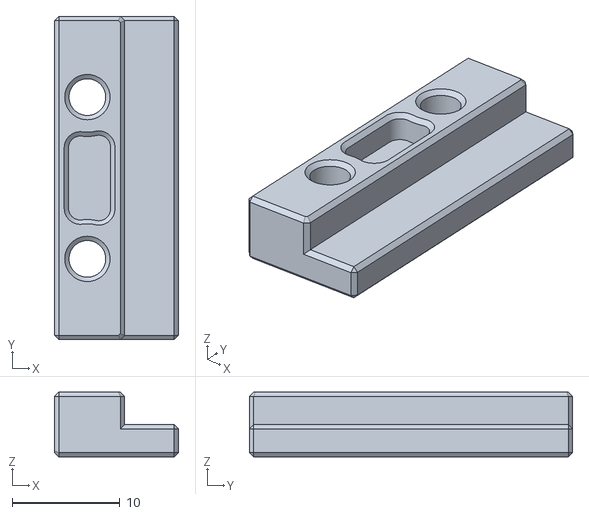
[picture p75: CAD file, 2025-04-02]
STLs/V0/Electronics/Fan_Mount_Top_x1.stl
11.5 x 30.0 x 6.00
