3lkgrove/VoronZero/STLs/V0/Panel_Mounting/Front_Bottom_Right_Hinge_x1.stl

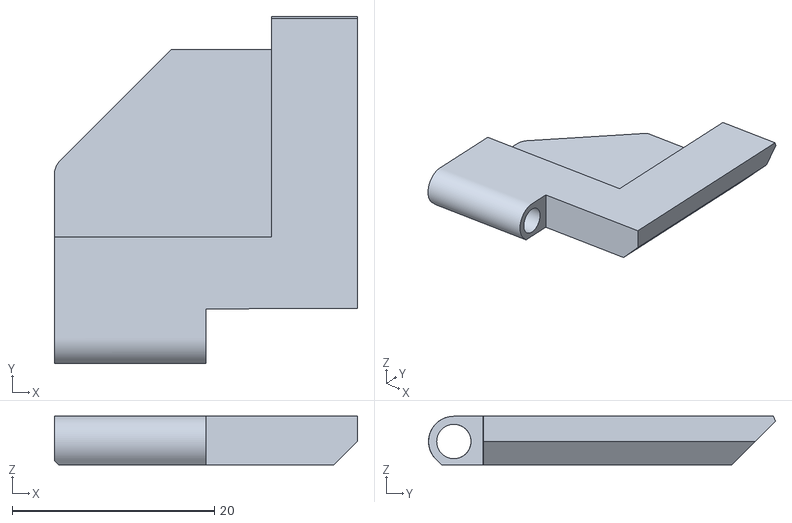
[picture p76: CAD file, 2025-04-02]
STLs/V0/Panel_Mounting/Front_Bottom_Right_Hinge_x1.stl
30.0 x 34.3 x 4.80
