3lkgrove/VoronZero/STLs/V0/Toolheads/Hotend_Mounts/Standard/[a]_Hotend_Mount_Dragonfly_BMS_7_FINS.stl

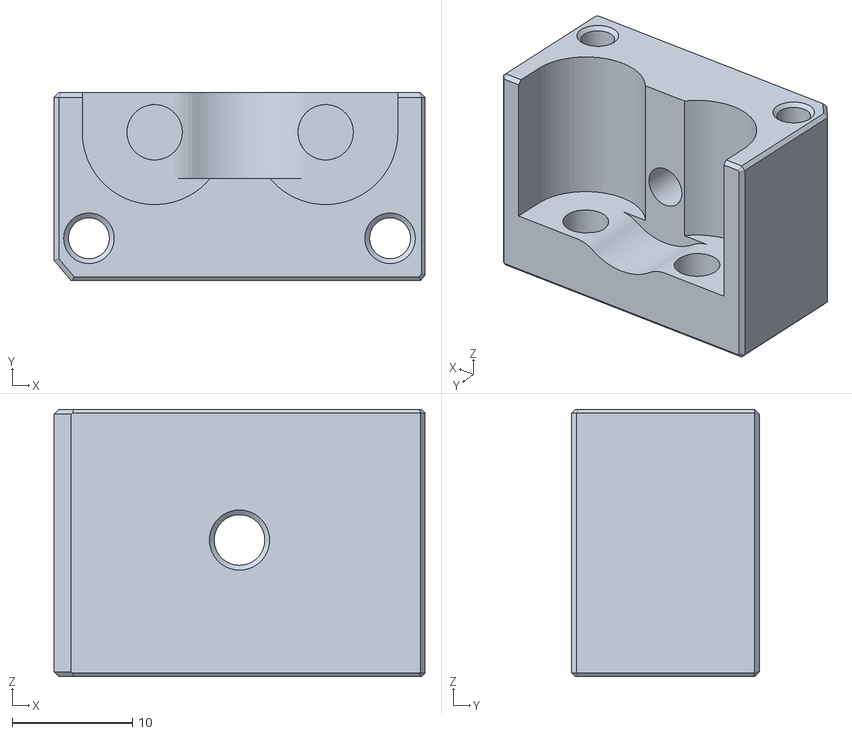
[picture p77: CAD file, 2025-04-02]
STLs/V0/Toolheads/Hotend_Mounts/Standard/[a]_Hotend_Mount_Dragonfly_BMS_7_FINS.stl
30.8 x 15.6 x 22.2
