3lkgrove/VoronZero/STLs/V0/Toolheads/Mini_Stealthburner/Strain_Relief_Body_x1.stl

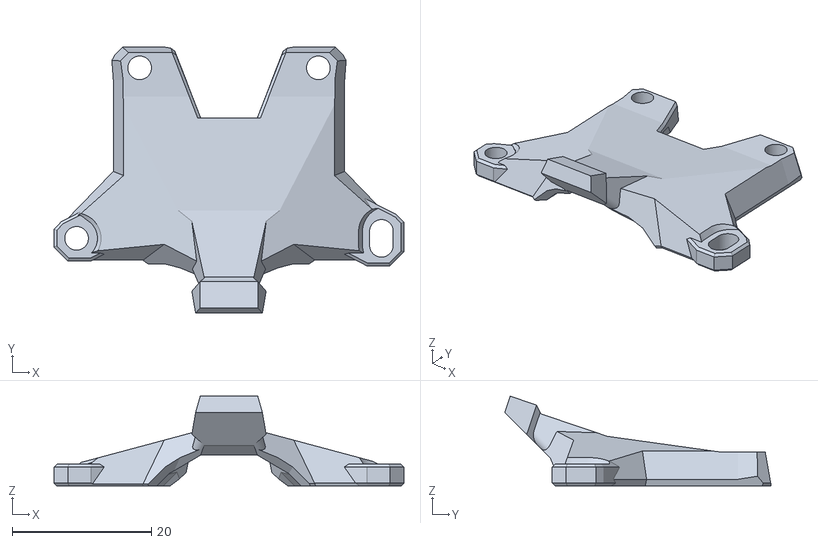
[picture p78: CAD file, 2025-04-02]
STLs/V0/Toolheads/Mini_Stealthburner/Strain_Relief_Body_x1.stl
50.3 x 38.3 x 12.9
