3lkgrove/VoronZero/STLs/Kirigami/VORON_v0.2_belt_chain_mount.stl

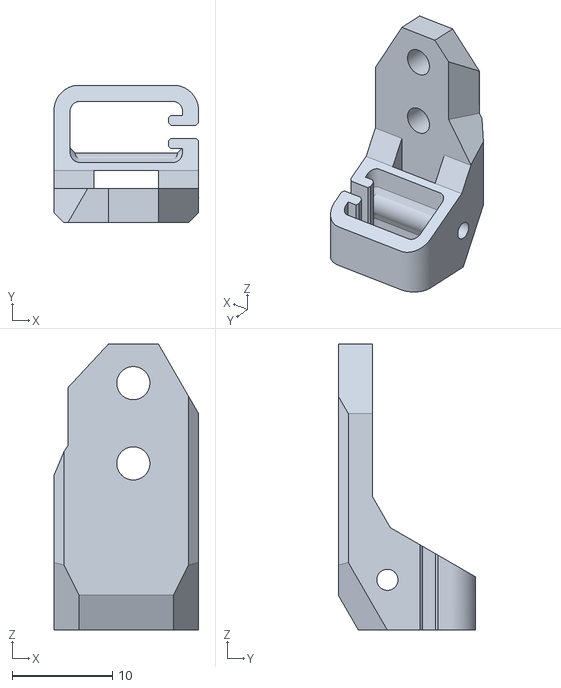
[picture p79: CAD file, 2025-04-02]
STLs/Kirigami/VORON_v0.2_belt_chain_mount.stl
14.4 x 13.7 x 28.5
