3lkgrove/VoronZero/STLs/V0/Electronics/Manta_M4P_Din_Mount_2pc.stl

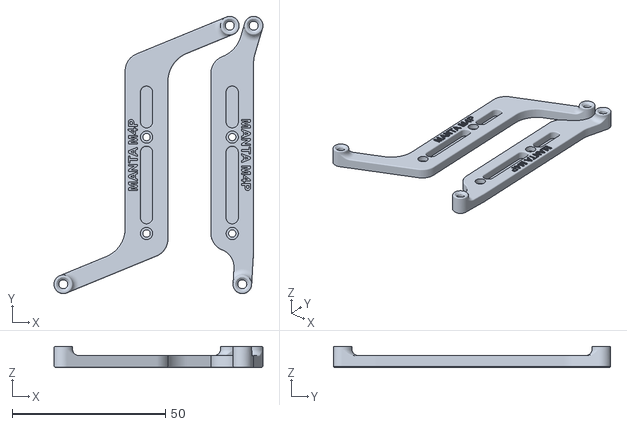
[picture p80: CAD file, 2025-04-02]
STLs/V0/Electronics/Manta_M4P_Din_Mount_2pc.stl
68.3 x 90.6 x 7.00
