3lkgrove/VoronZero/STLs/V0/Skirts/Foot_Front_Left_x1.STL

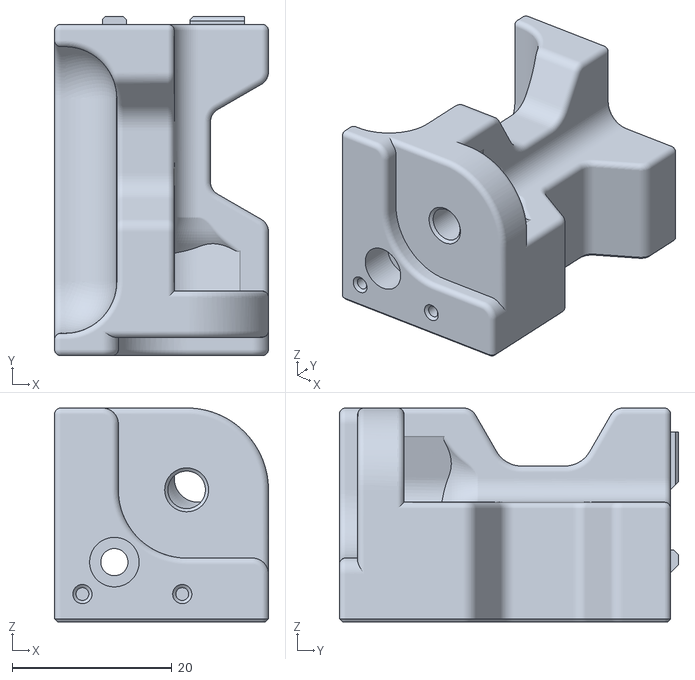
[picture p81: CAD file, 2025-04-02]
STLs/V0/Skirts/Foot_Front_Left_x1.STL
26.8 x 42.5 x 26.8
