3lkgrove/VoronZero/STLs/V0/Tophat/TH_Top_Clip_x4.stl

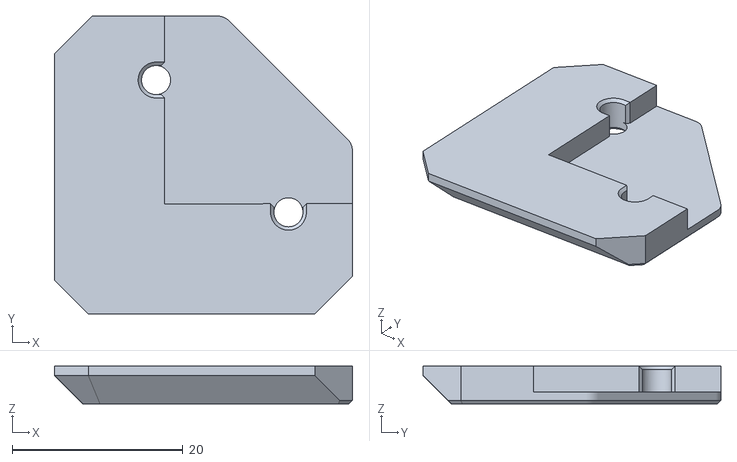
[picture p83: CAD file, 2025-04-02]
STLs/V0/Tophat/TH_Top_Clip_x4.stl
34.9 x 34.9 x 4.40
