3lkgrove/VoronZero/STLs/V0/X_Carriage_x1.stl

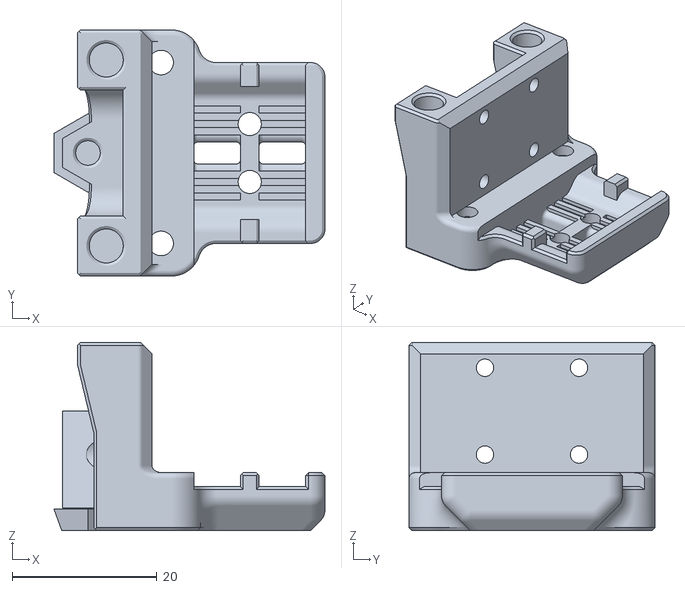
[picture p84: CAD file, 2025-04-02]
STLs/V0/X_Carriage_x1.stl
37.5 x 34.0 x 26.0
