3lkgrove/VoronZero/STLs/Kirigami/VORON_v0.2_stealth_wire_guide.stl

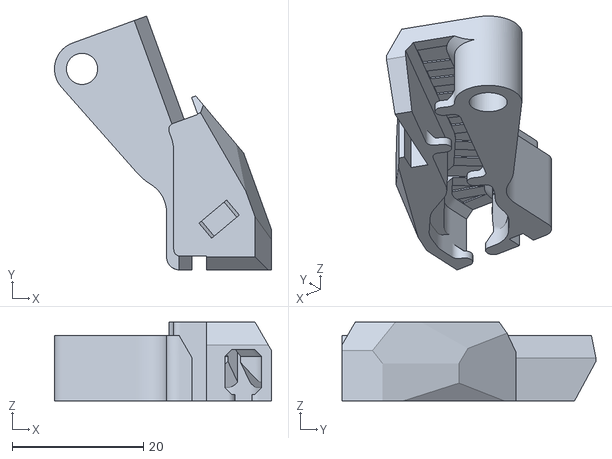
[picture p85: CAD file, 2025-04-02]
STLs/Kirigami/VORON_v0.2_stealth_wire_guide.stl
33.1 x 38.7 x 12.0
