3lkgrove/VoronZero/STLs/V0/Electronics/[a]_Cable_Tie_x1.stl

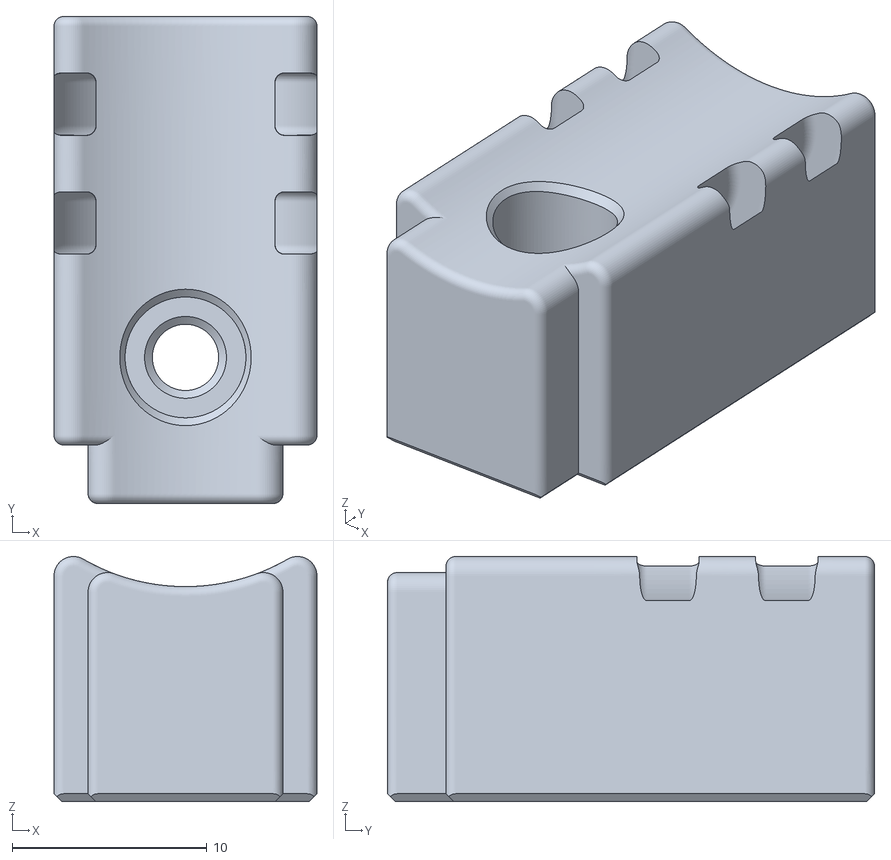
[picture p86: CAD file, 2025-04-02]
STLs/V0/Electronics/[a]_Cable_Tie_x1.stl
13.5 x 25.0 x 12.6
