3lkgrove/VoronZero/STLs/V0/Panel_Mounting/Right_Top_Left_Hinge_x1.stl

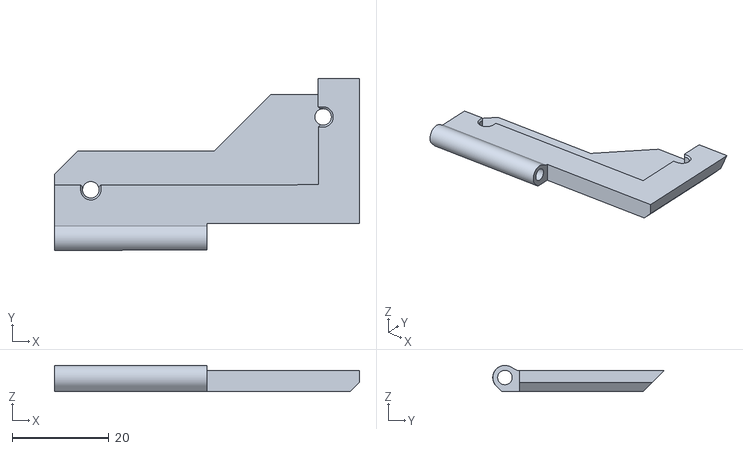
[picture p87: CAD file, 2025-04-02]
STLs/V0/Panel_Mounting/Right_Top_Left_Hinge_x1.stl
63.0 x 35.5 x 5.40
