3lkgrove/VoronZero/STLs/V0/Skirts/[a]_Foot_Accent_A_x2.stl

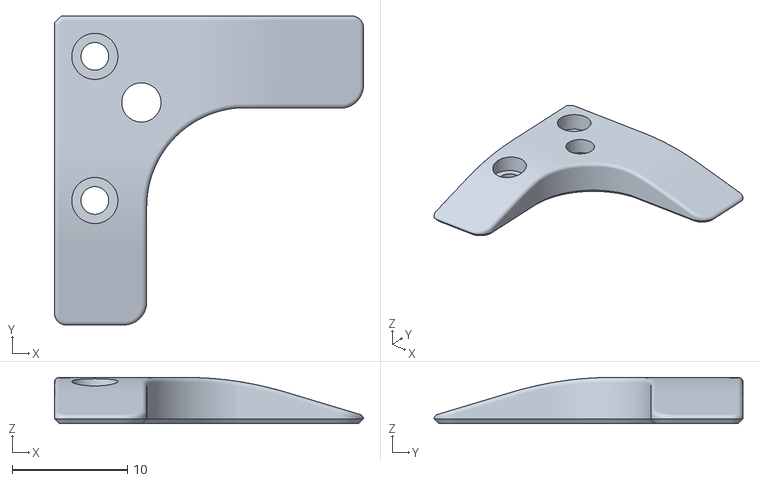
[picture p88: CAD file, 2025-04-02]
STLs/V0/Skirts/[a]_Foot_Accent_A_x2.stl
26.8 x 26.8 x 4.00
