3lkgrove/VoronZero/STLs/V0/B_Idler_Upper_x1.stl

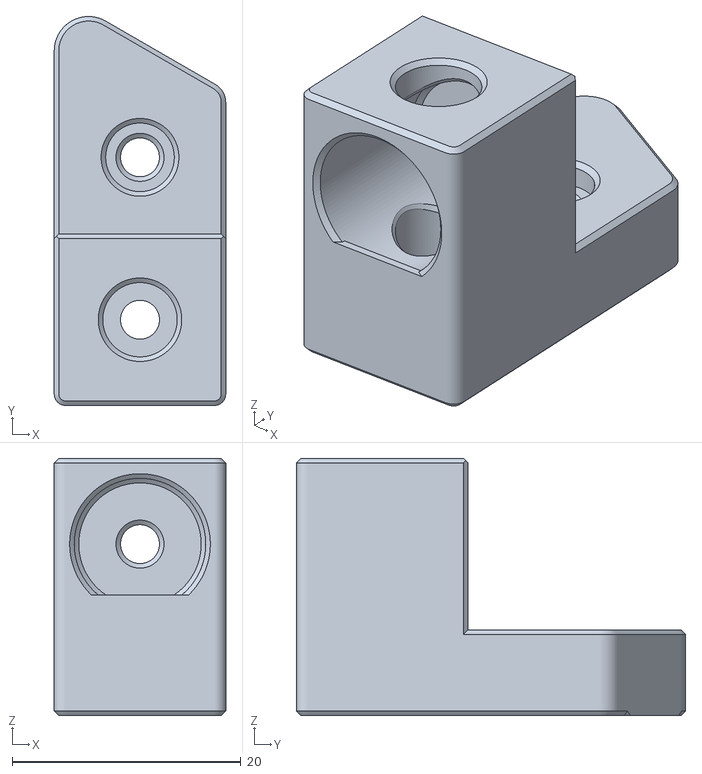
[picture p90: CAD file, 2025-04-02]
STLs/V0/B_Idler_Upper_x1.stl
15.0 x 34.0 x 22.5
