3lkgrove/VoronZero/STLs/V0/Electronics/VHB_DIN_Mount.STL

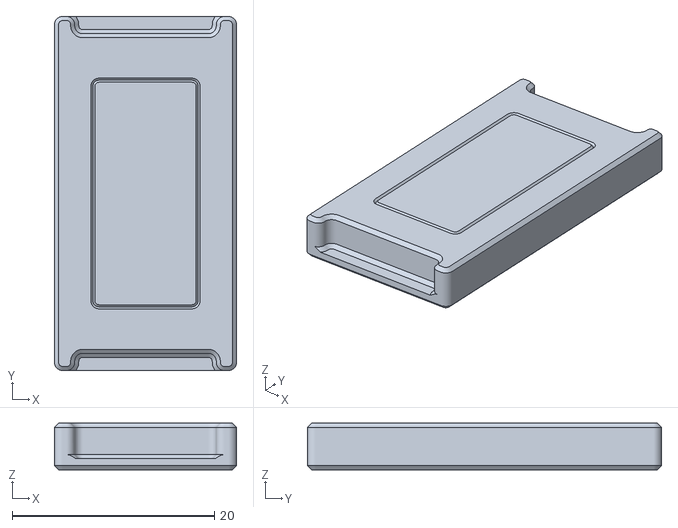
[picture p91: CAD file, 2025-04-02]
STLs/V0/Electronics/VHB_DIN_Mount.STL
18.0 x 35.0 x 4.60
