3lkgrove/VoronZero/STLs/V0/Skirts/Headless_Skirt_Insert.STL

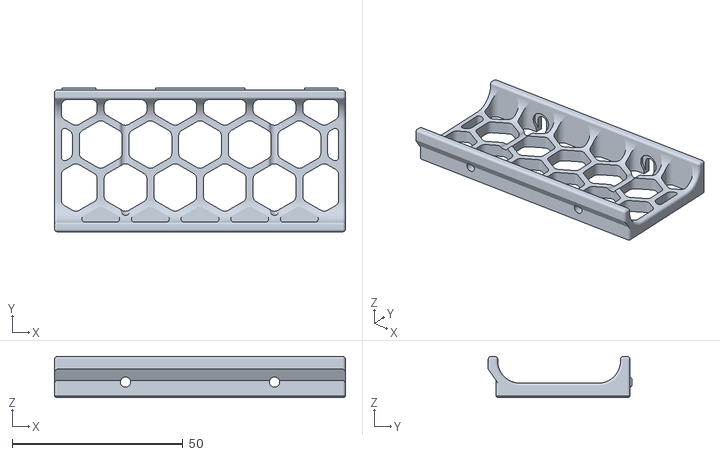
[picture p92: CAD file, 2025-04-02]
STLs/V0/Skirts/Headless_Skirt_Insert.STL
85.2 x 42.0 x 12.0
