3lkgrove/VoronZero/STLs/V0/Electronics/PCB_DIN_Clip_x2.stl

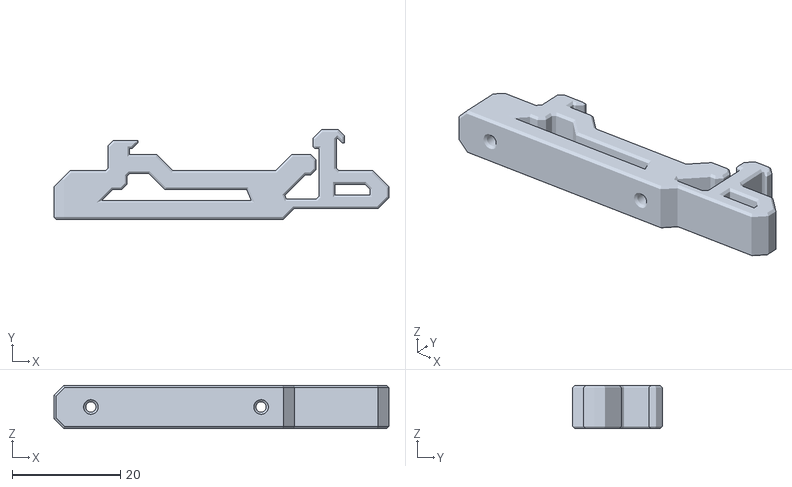
[picture p93: CAD file, 2025-04-02]
STLs/V0/Electronics/PCB_DIN_Clip_x2.stl
62.0 x 16.6 x 8.00
