3lkgrove/VoronZero/STLs/V0/Electronics/SKR_3_EZ_Din_Mount.stl

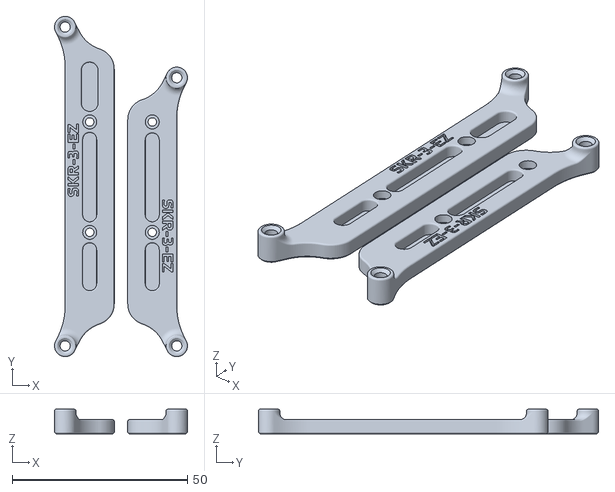
[picture p94: CAD file, 2025-04-02]
STLs/V0/Electronics/SKR_3_EZ_Din_Mount.stl
37.9 x 97.1 x 7.00
