3lkgrove/VoronZero/STLs/V0/Panel_Mounting/Front_Top_Left_Clip_x1.stl

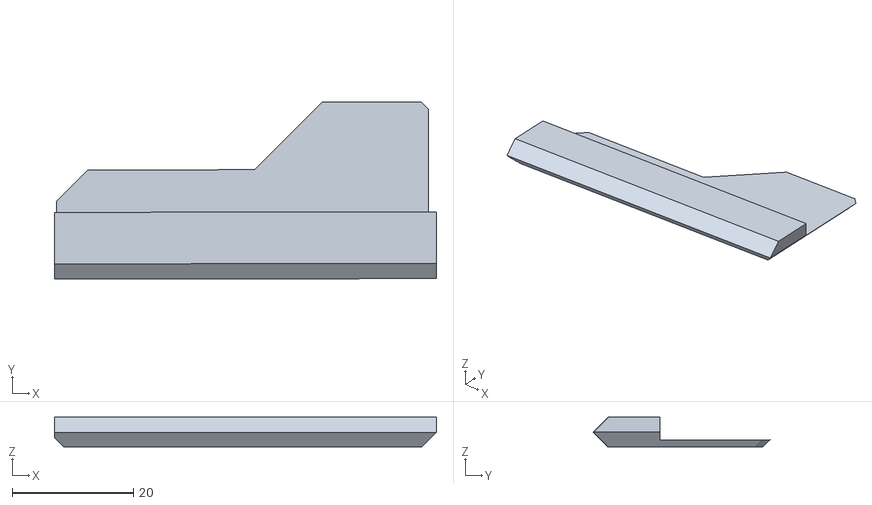
[picture p95: CAD file, 2025-04-02]
STLs/V0/Panel_Mounting/Front_Top_Left_Clip_x1.stl
63.0 x 29.2 x 4.90
