3lkgrove/VoronZero/STLs/V0/A_Idler_Upper_x1.stl

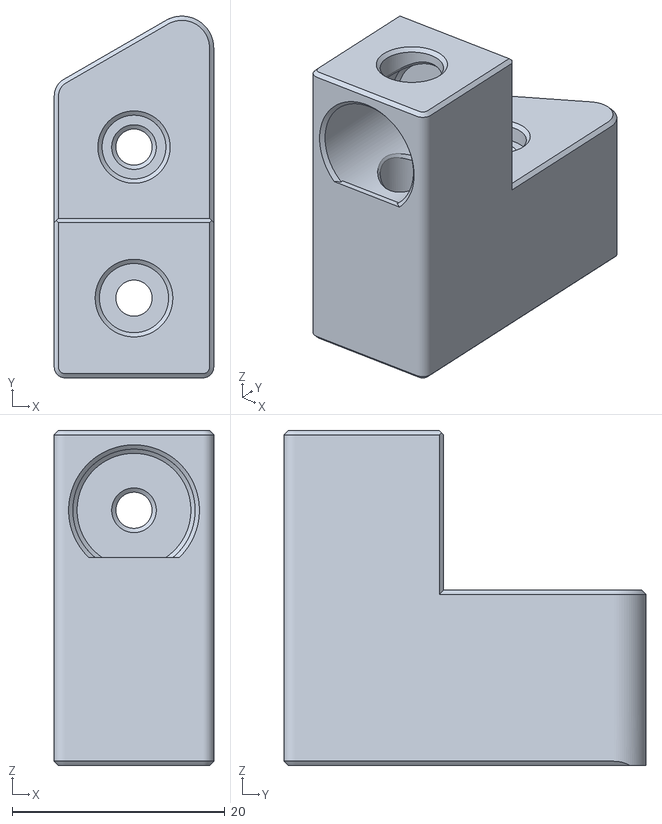
[picture p96: CAD file, 2025-04-02]
STLs/V0/A_Idler_Upper_x1.stl
15.0 x 34.0 x 31.5
