3lkgrove/VoronZero/STLs/V0/[a]_Z_Endstop_Mount_x1.STL

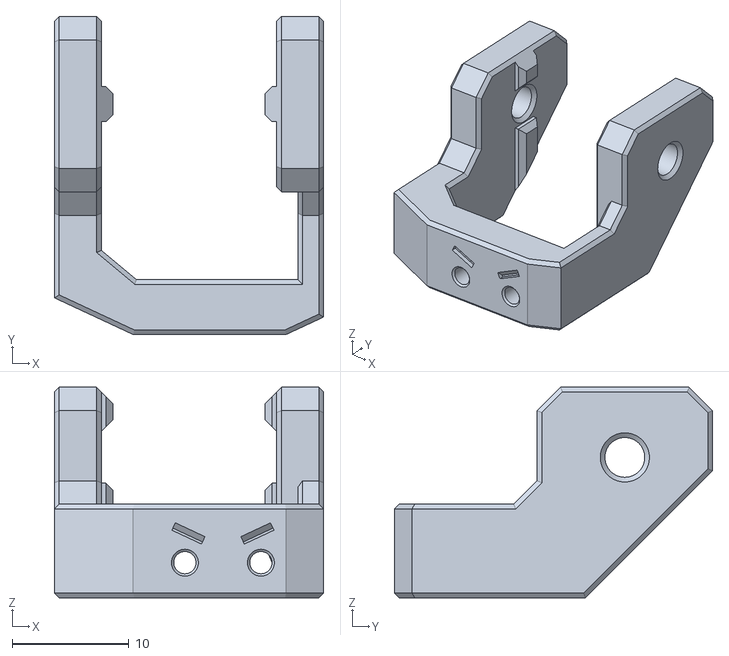
[picture p97: CAD file, 2025-04-02]
STLs/V0/[a]_Z_Endstop_Mount_x1.STL
23.0 x 27.2 x 18.0
