3lkgrove/VoronZero/STLs/V0/Panel_Mounting/Middle_Clip_x9.stl

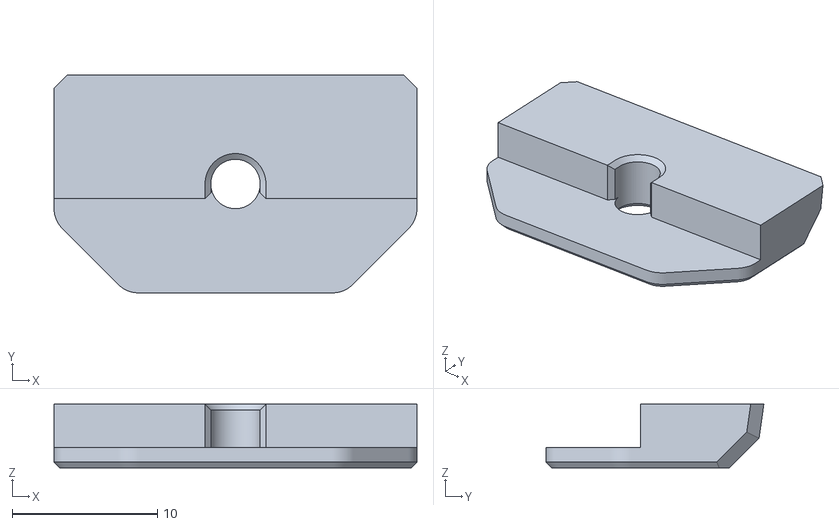
[picture p98: CAD file, 2025-04-02]
STLs/V0/Panel_Mounting/Middle_Clip_x9.stl
25.0 x 15.0 x 4.40
