3lkgrove/VoronZero/STLs/V0/Skirts/Rear_Skirt_x1.STL

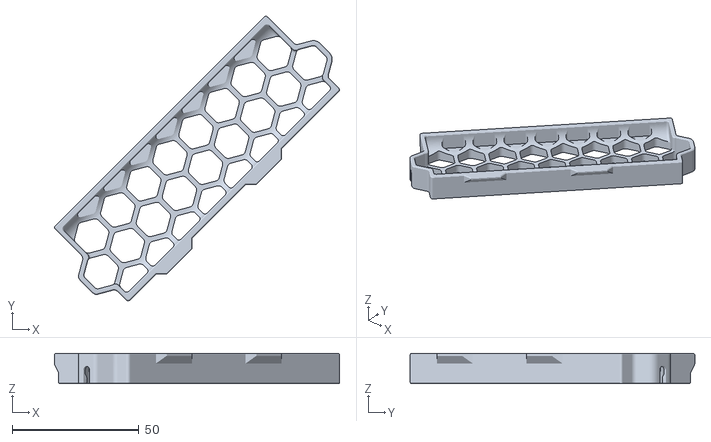
[picture p99: CAD file, 2025-04-02]
STLs/V0/Skirts/Rear_Skirt_x1.STL
112.3 x 112.1 x 12.0
