3lkgrove/VoronZero/STLs/V0/[a]_A_Drive_Tensioner_x1.stl

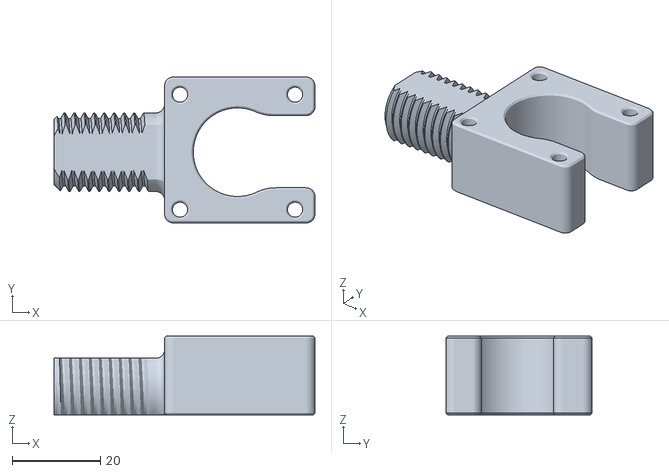
[picture p100: CAD file, 2025-04-02]
STLs/V0/[a]_A_Drive_Tensioner_x1.stl
59.0 x 33.0 x 17.8
