3lkgrove/VoronZero/STLs/V0/Panel_Mounting/Door_Latch_x2.STL

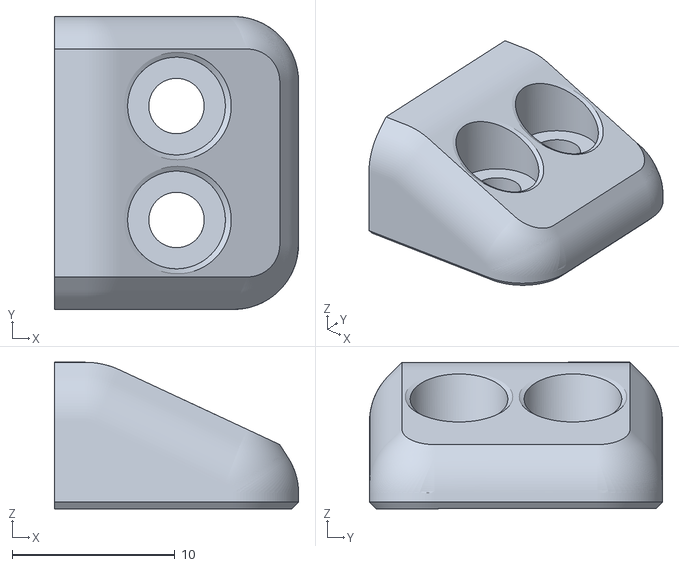
[picture p101: CAD file, 2025-04-02]
STLs/V0/Panel_Mounting/Door_Latch_x2.STL
15.0 x 18.0 x 9.00
