3lkgrove/VoronZero/STLs/V0/Panel_Mounting/Rear_Bottom_Right_Clip_x1.stl

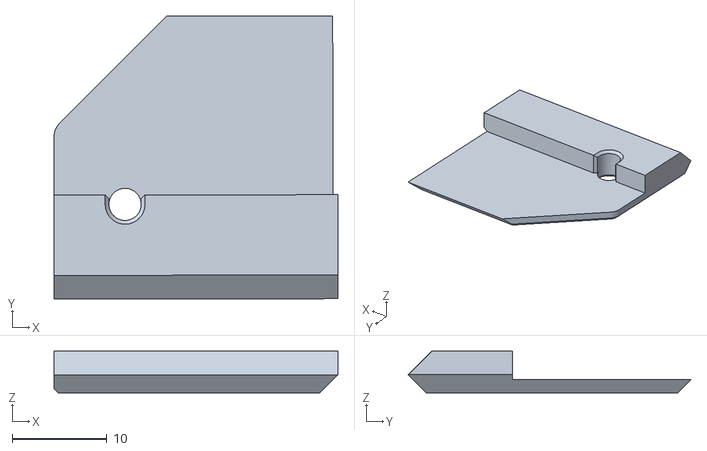
[picture p102: CAD file, 2025-04-02]
STLs/V0/Panel_Mounting/Rear_Bottom_Right_Clip_x1.stl
30.0 x 29.9 x 4.40
