3lkgrove/VoronZero/STLs/V0/Rear_Bed_Mount_Left_x1.stl

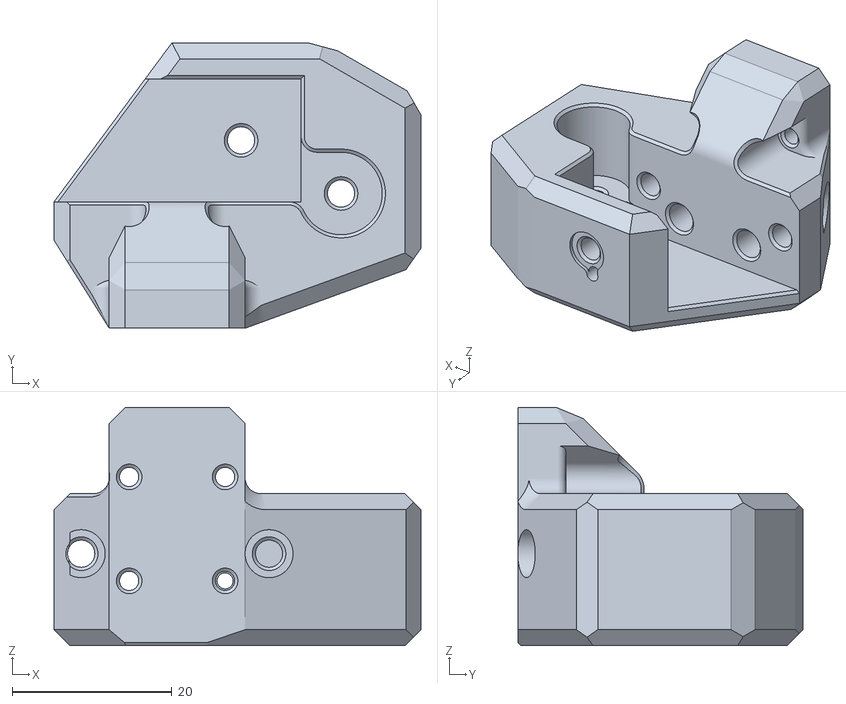
[picture p103: CAD file, 2025-04-02]
STLs/V0/Rear_Bed_Mount_Left_x1.stl
45.9 x 35.7 x 29.8
