3lkgrove/VoronZero/STLs/V0/[a]_Tensioner_Knob_x2.stl

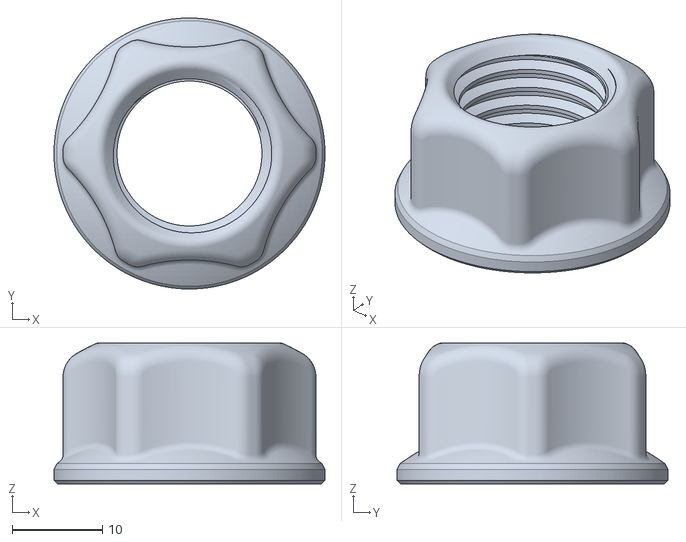
[picture p104: CAD file, 2025-04-02]
STLs/V0/[a]_Tensioner_Knob_x2.stl
30.0 x 30.0 x 15.6
