3lkgrove/VoronZero/STLs/V0/[a]_Railstops_x5.stl

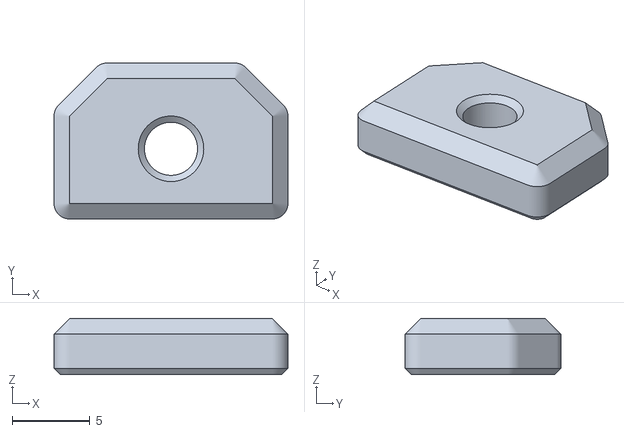
[picture p105: CAD file, 2025-04-02]
STLs/V0/[a]_Railstops_x5.stl
15.0 x 10.0 x 3.60
