3lkgrove/VoronZero/STLs/V0/[a]_Z_Motor_Mount_x1.stl

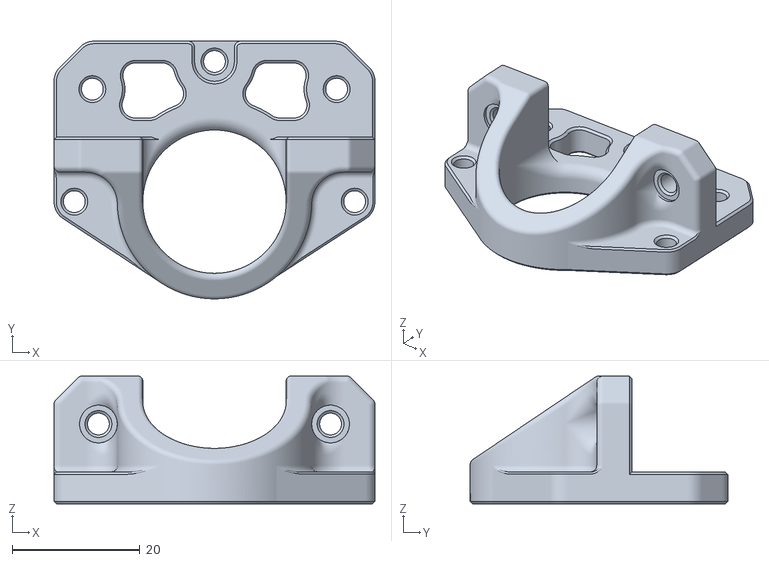
[picture p106: CAD file, 2025-04-02]
STLs/V0/[a]_Z_Motor_Mount_x1.stl
50.2 x 40.3 x 20.0
