3lkgrove/VoronZero/STLs/V0/B_Idler_Lower_x1.stl

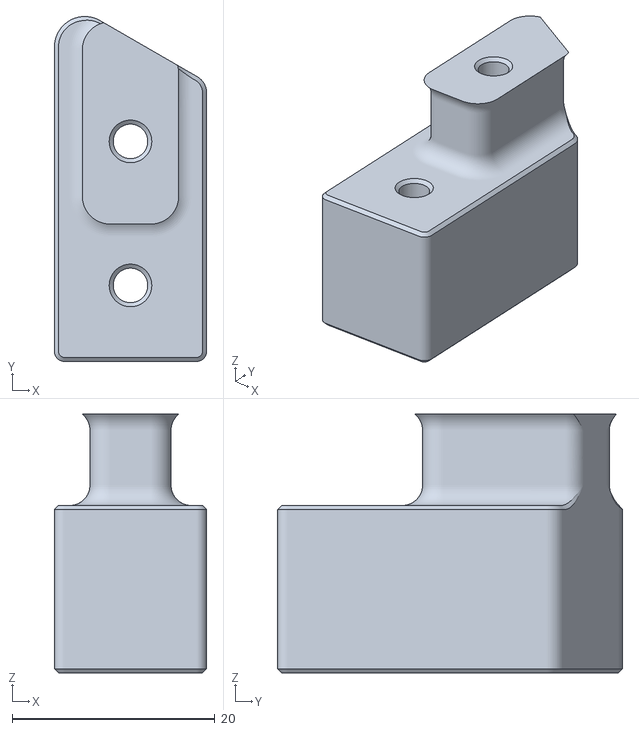
[picture p107: CAD file, 2025-04-02]
STLs/V0/B_Idler_Lower_x1.stl
15.0 x 34.0 x 25.5
