3lkgrove/VoronZero/STLs/V0/[a]_Idler_Cam_Lock_x2.STL

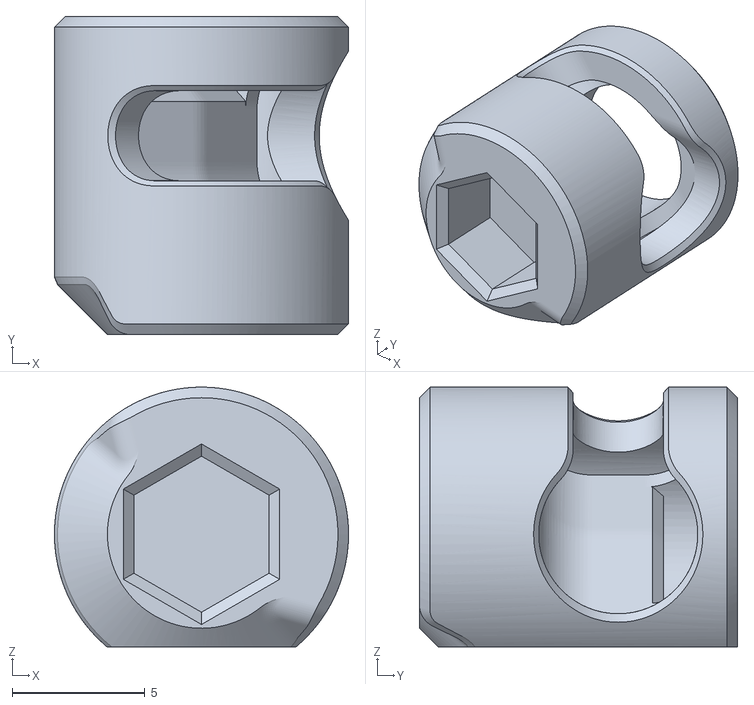
[picture p108: CAD file, 2025-04-02]
STLs/V0/[a]_Idler_Cam_Lock_x2.STL
11.1 x 12.0 x 9.80
