3lkgrove/VoronZero/STLs/V0/A_Idler_Lower_x1.stl

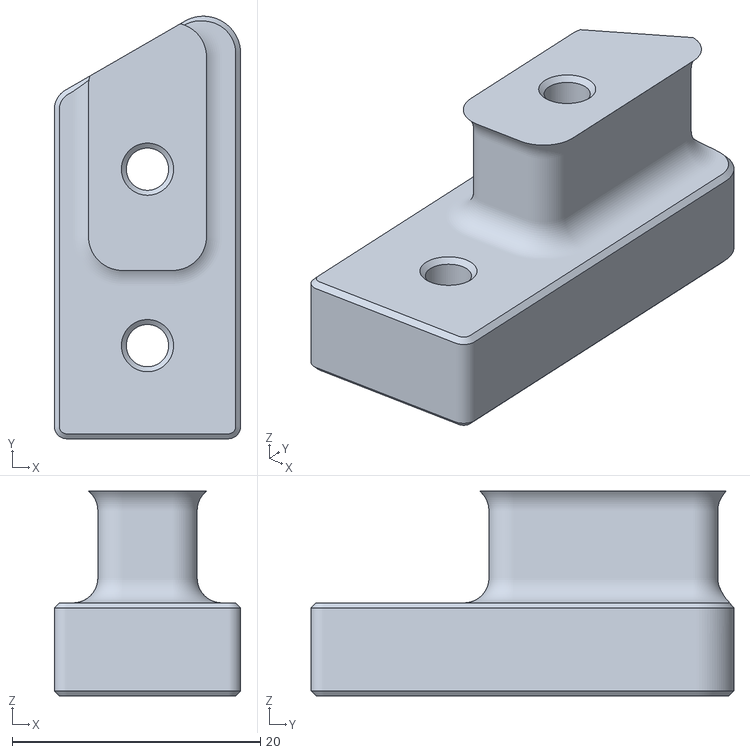
[picture p109: CAD file, 2025-04-02]
STLs/V0/A_Idler_Lower_x1.stl
15.0 x 34.0 x 16.5
