3lkgrove/VoronZero/STLs/V0/XY_Joint_Left_Upper_x1.stl

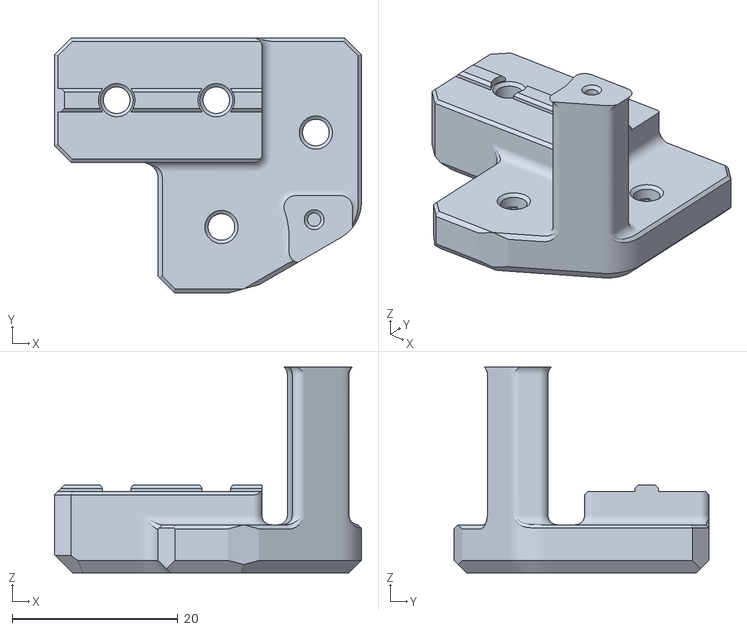
[picture p110: CAD file, 2025-04-02]
STLs/V0/XY_Joint_Left_Upper_x1.stl
37.0 x 30.7 x 24.8
