3lkgrove/VoronZero/STLs/V0/Rear_Bed_Mount_Right_x1.stl

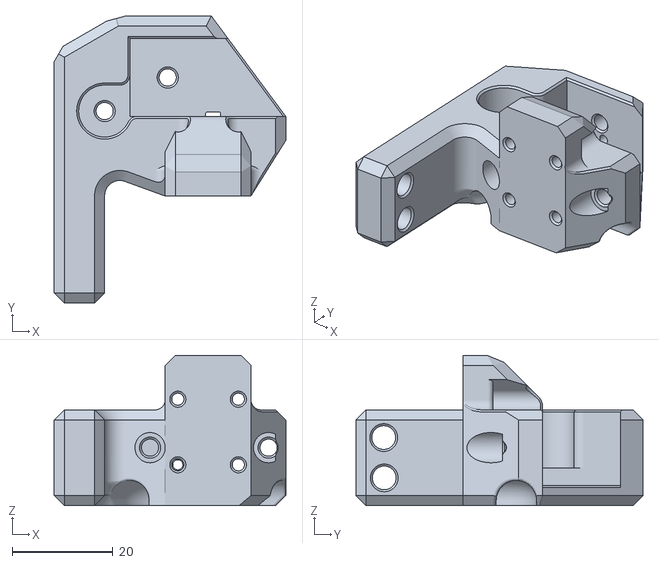
[picture p111: CAD file, 2025-04-02]
STLs/V0/Rear_Bed_Mount_Right_x1.stl
45.9 x 56.9 x 29.8
