3lkgrove/VoronZero/STLs/V0/Drag_Chain_Spacer_x1.stl

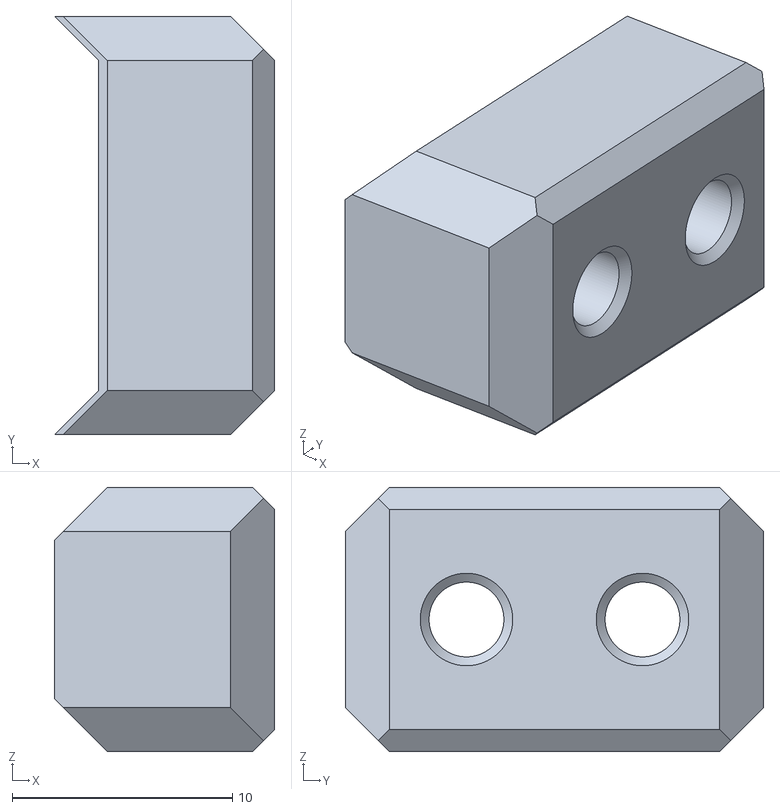
[picture p112: CAD file, 2025-04-02]
STLs/V0/Drag_Chain_Spacer_x1.stl
10.0 x 19.0 x 12.0
